aorfi/URA2019/Photos/iteration.docx

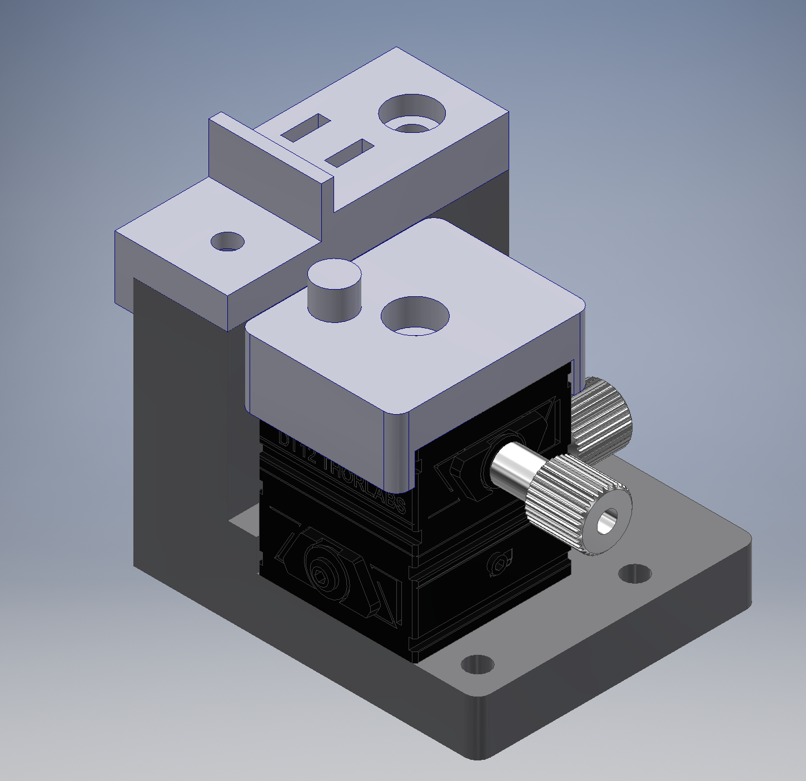
[picture p11: figure]
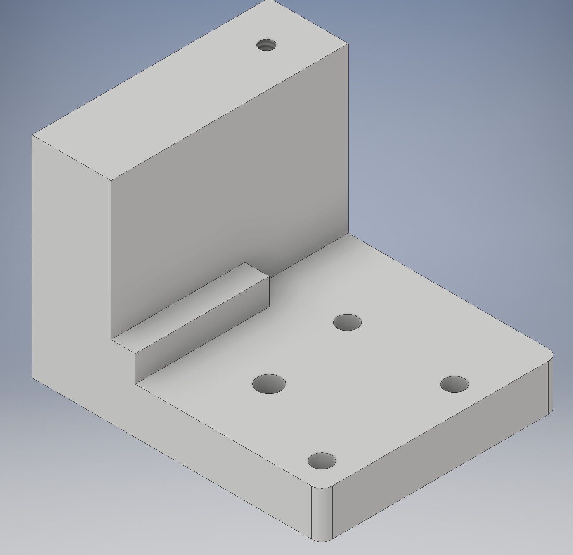
[picture p12: figure]
