aorfi/URA2019/Photos/Version2.docx

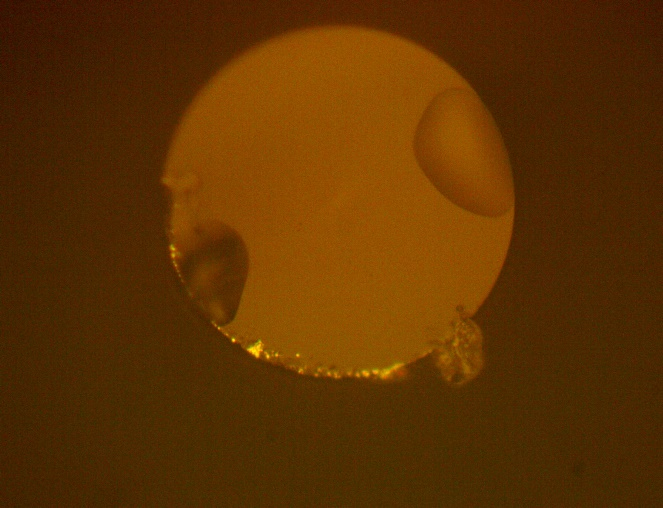
[picture p13: figure]
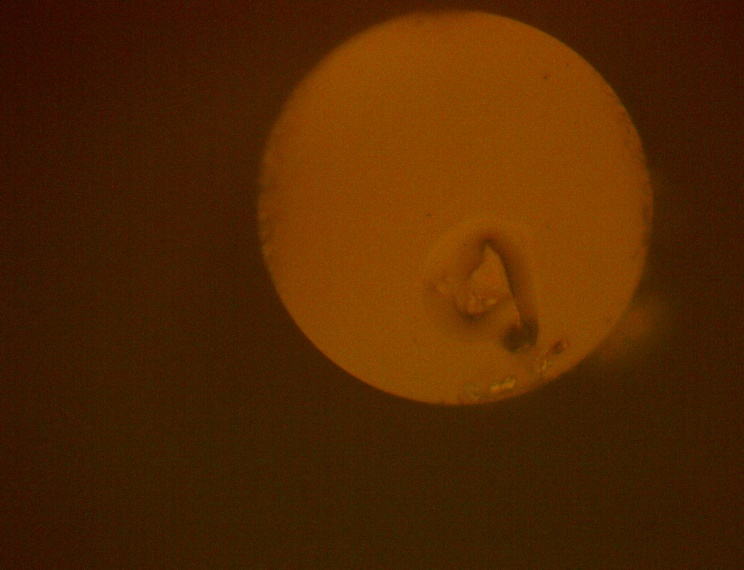
[picture p14: figure]
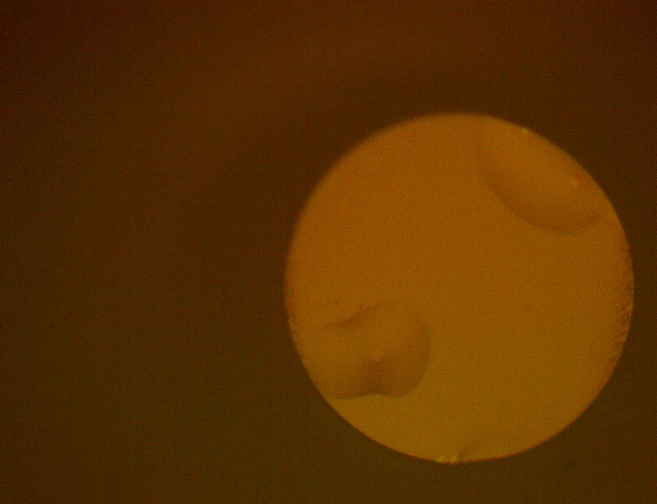
[picture p15: figure]
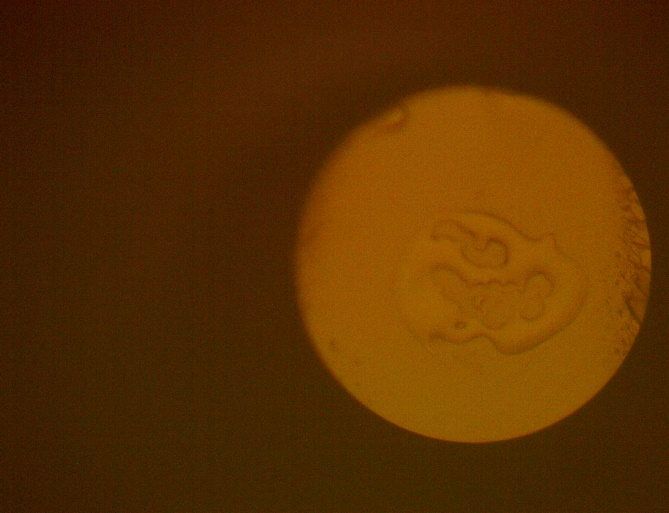
[picture p16: figure]
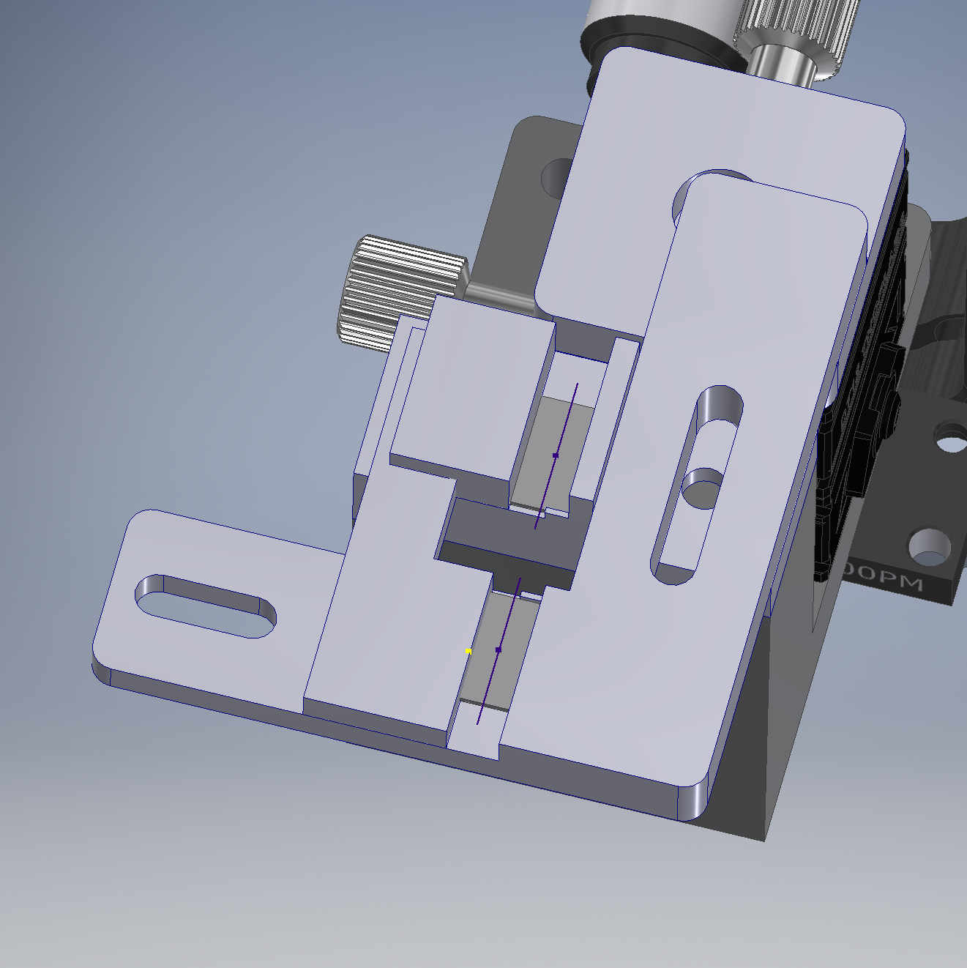
[picture p17: figure]
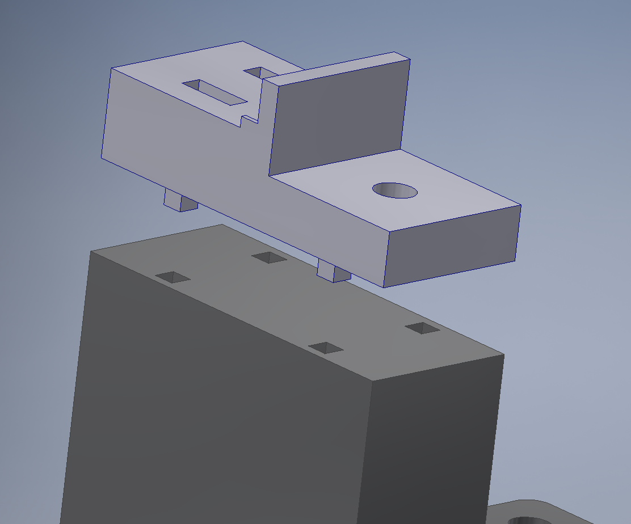
[picture p18: figure]
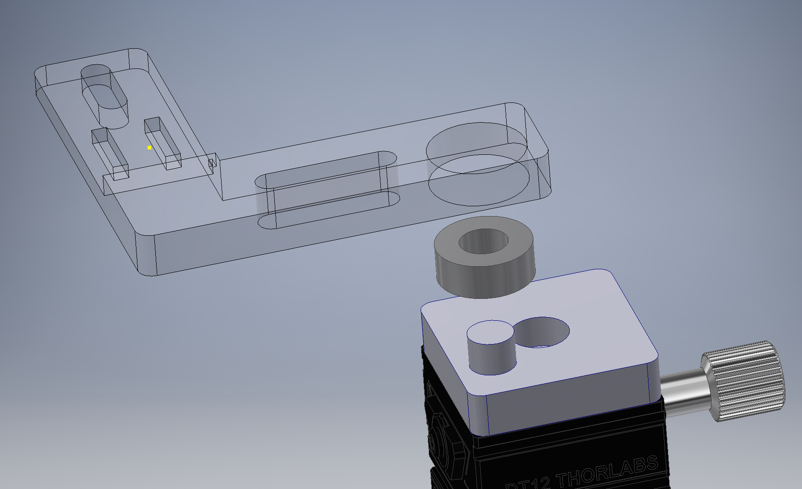
[picture p19: figure]
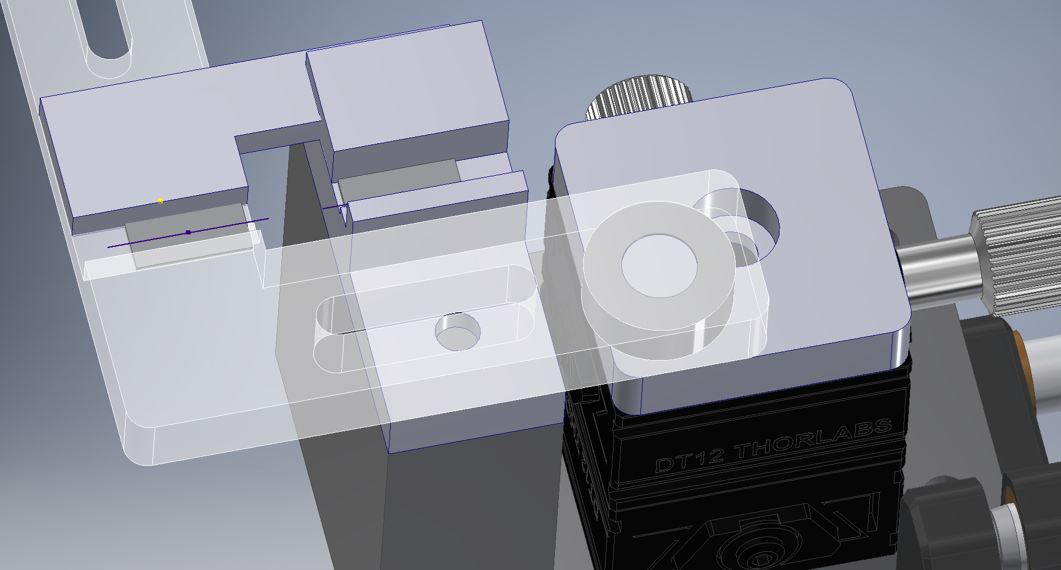
[picture p20: figure]
