aorfi/URA2019/Photos/Epoxy Stamp.docx

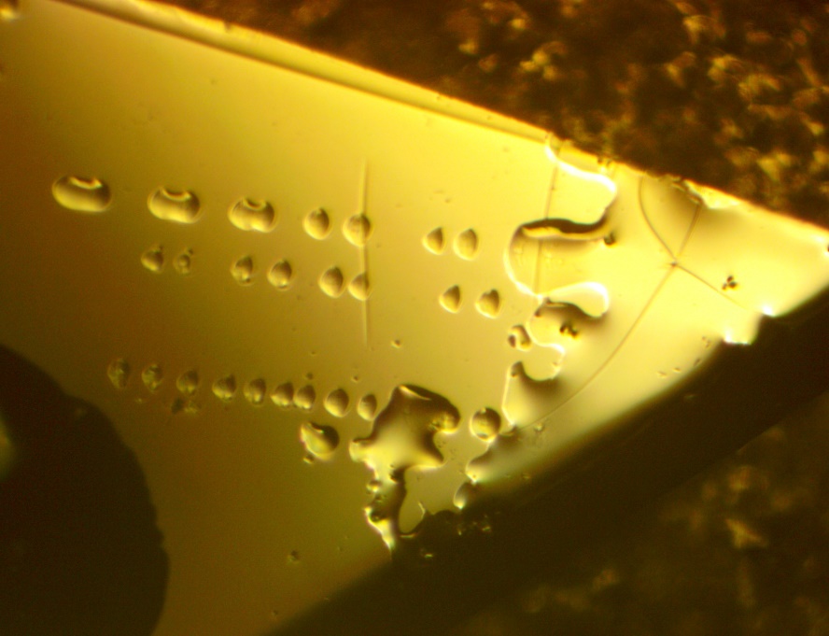
[picture p21: figure]
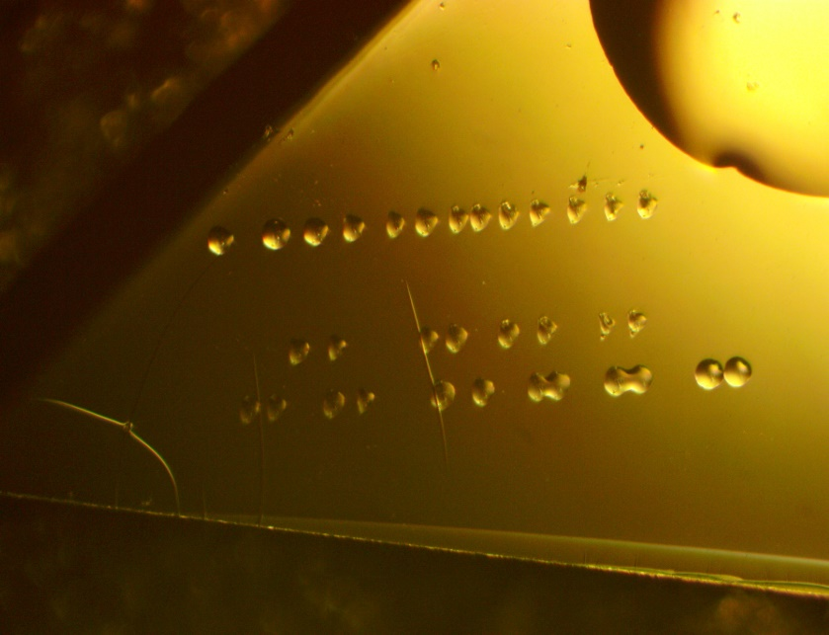
[picture p22: figure]
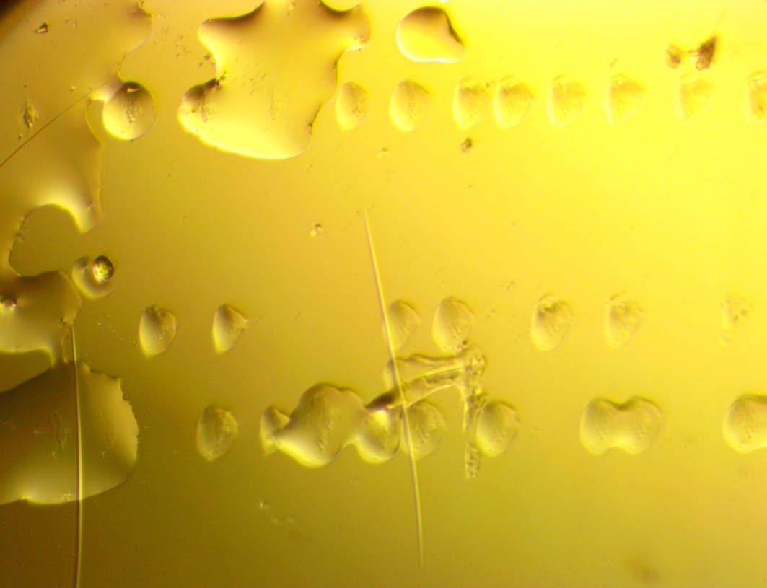
[picture p23: figure]
