aorfi/URA2019/Photos/LabBookPhotos.docx

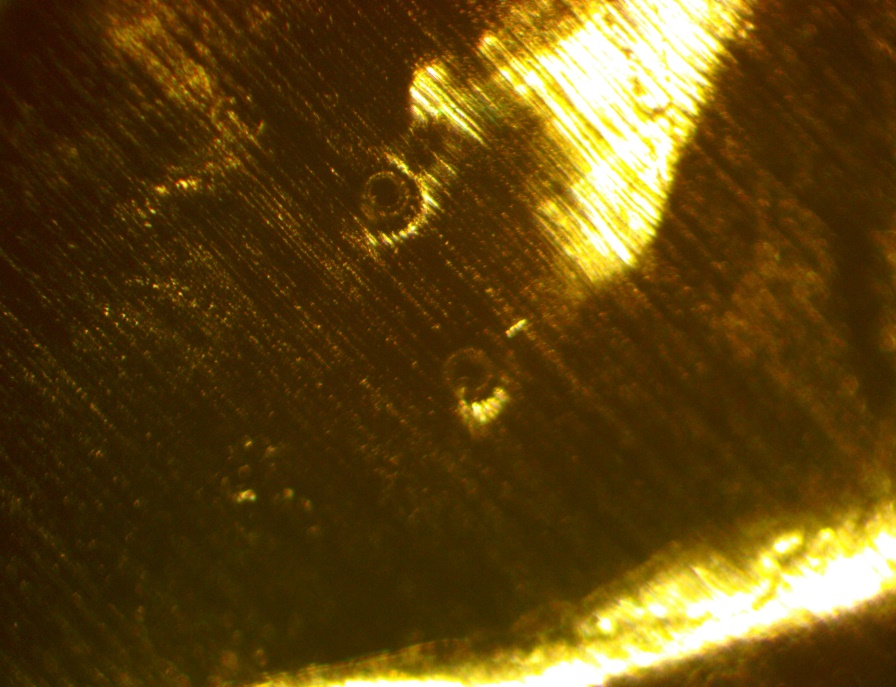
[picture p24: figure]
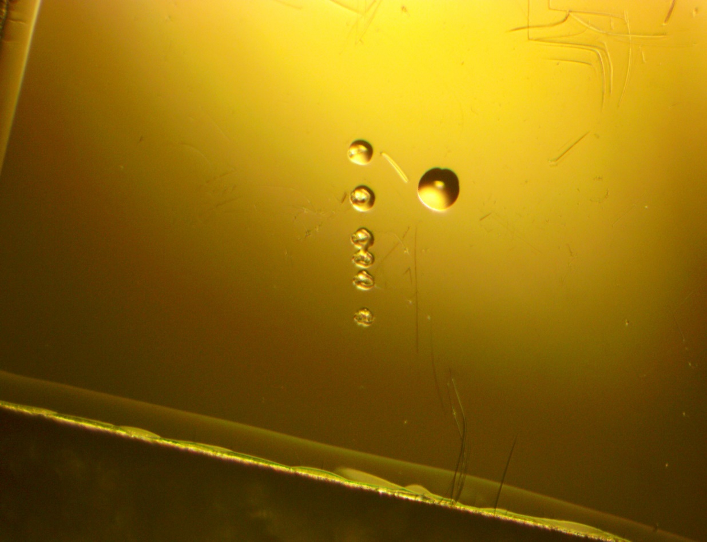
[picture p25: figure]
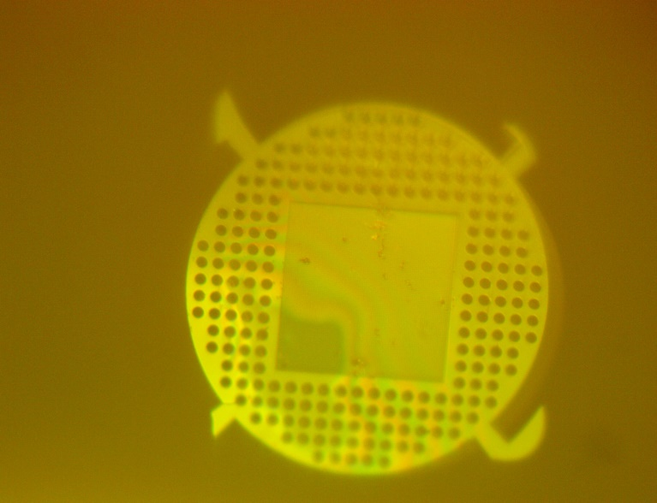
[picture p26: figure]
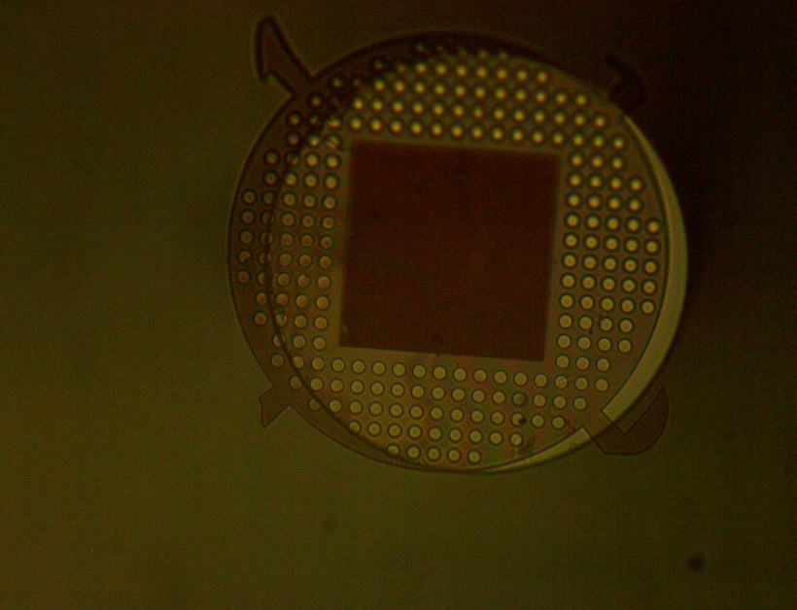
[picture p27: figure]
