aorfi/URA2019/Photos/02-1.jpg

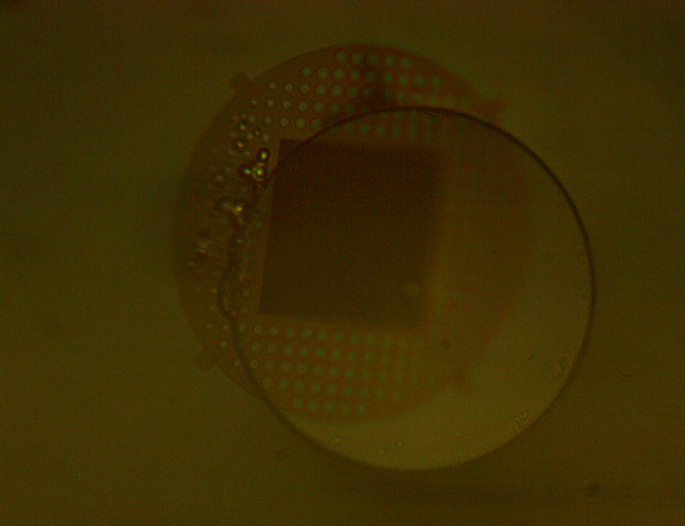
Photos/02-1.jpg
