aorfi/URA2019/Photos/02-2.jpg

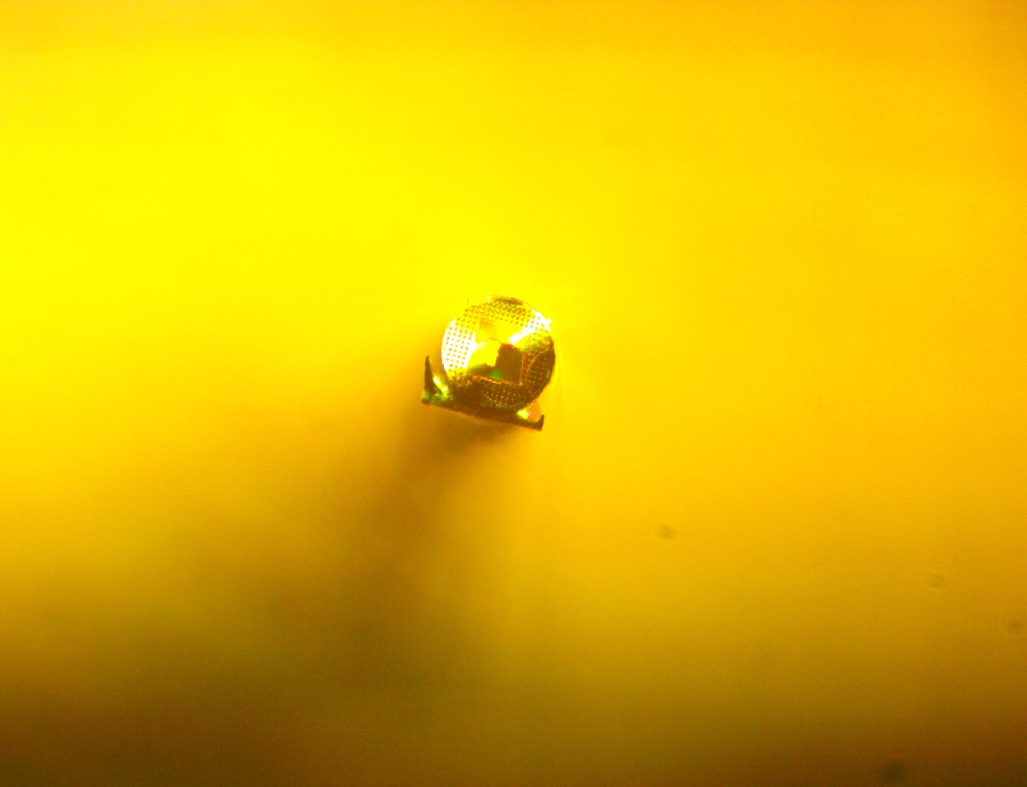
Photos/02-2.jpg
