aorfi/URA2019/Photos/03-1(1).jpg

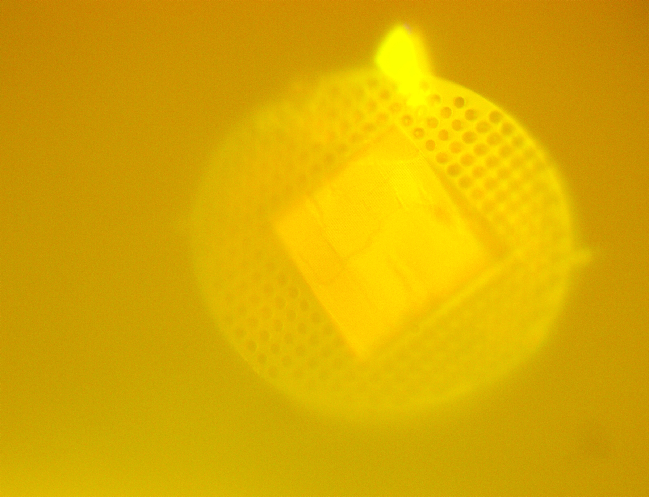
Photos/03-1(1).jpg
