aorfi/URA2019/Photos/03-Broken.jpg

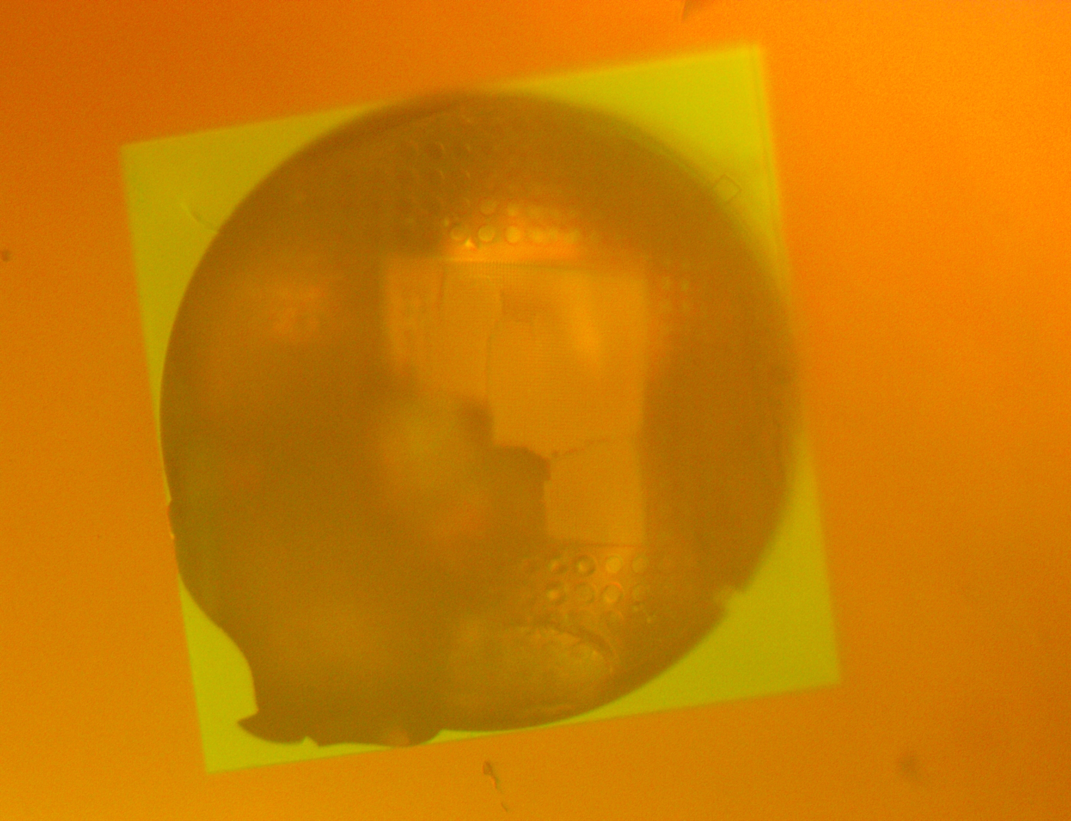
Photos/03-Broken.jpg
