aorfi/URA2019/Photos/aligned.JPG

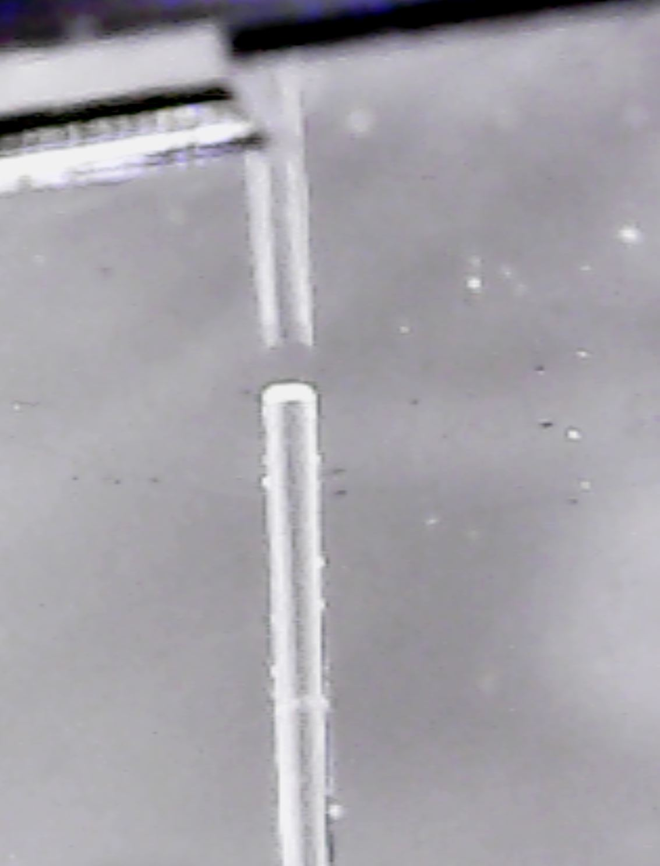
Photos/aligned.JPG
