aorfi/URA2019/Photos/ButtCouplingAfter2.jpg

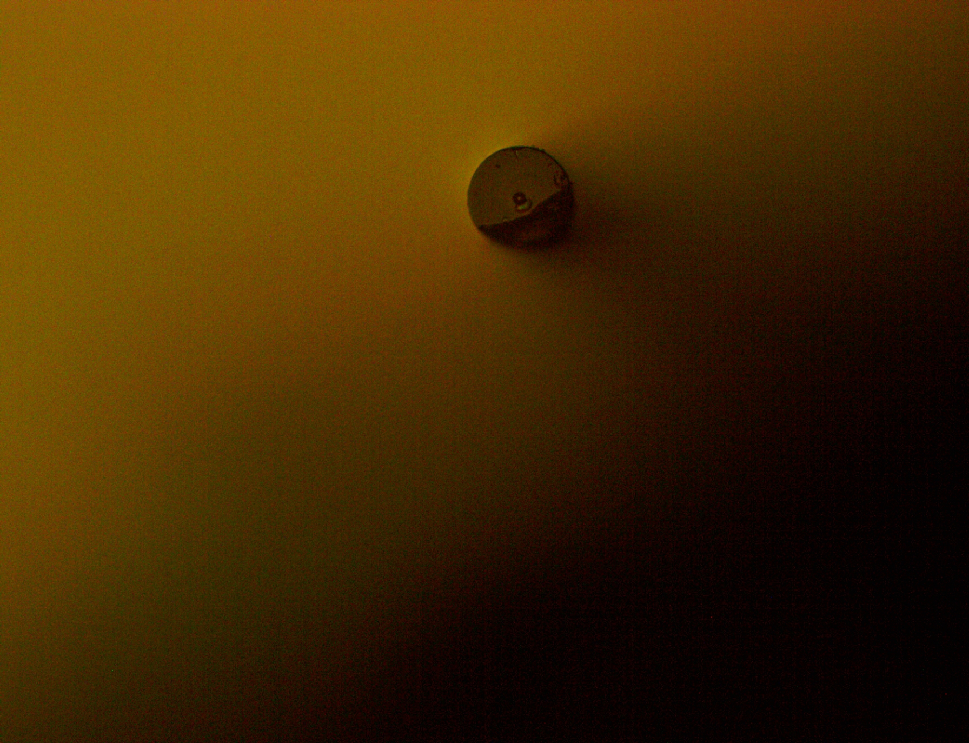
Photos/ButtCouplingAfter2.jpg
