aorfi/URA2019/Photos/ButtCouplingAfter4.jpg

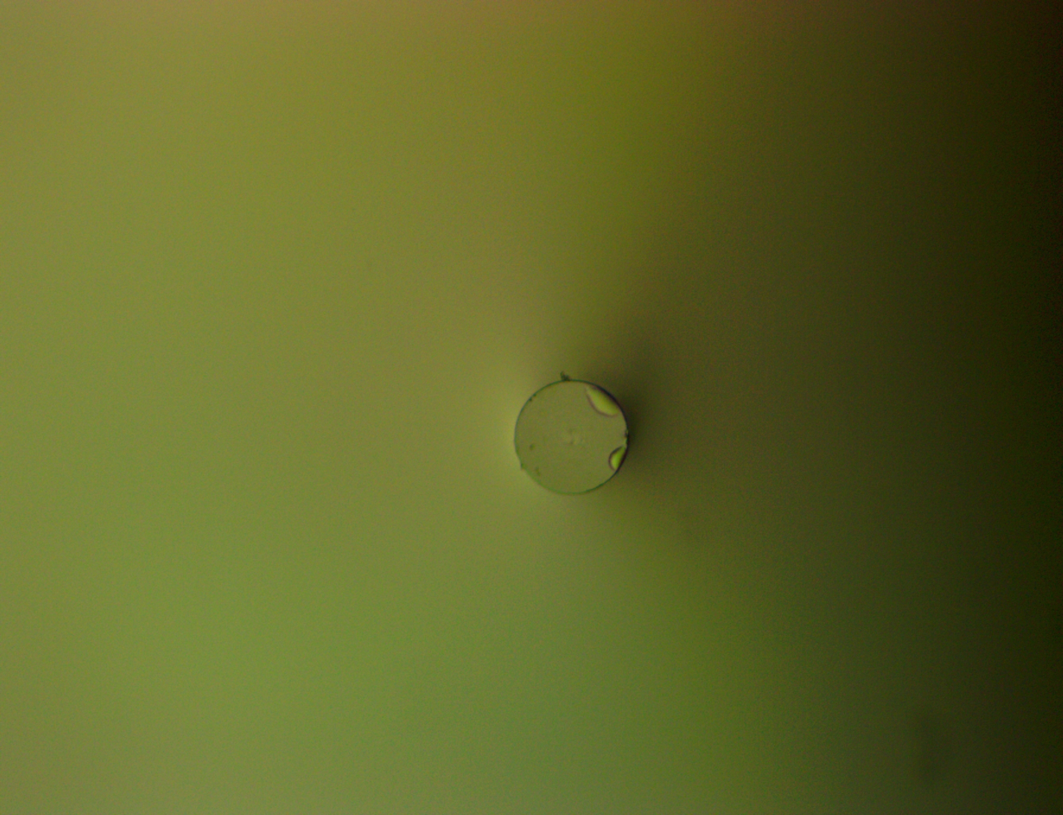
Photos/ButtCouplingAfter4.jpg
