aorfi/URA2019/Photos/ButtCouplingAfter5.jpg

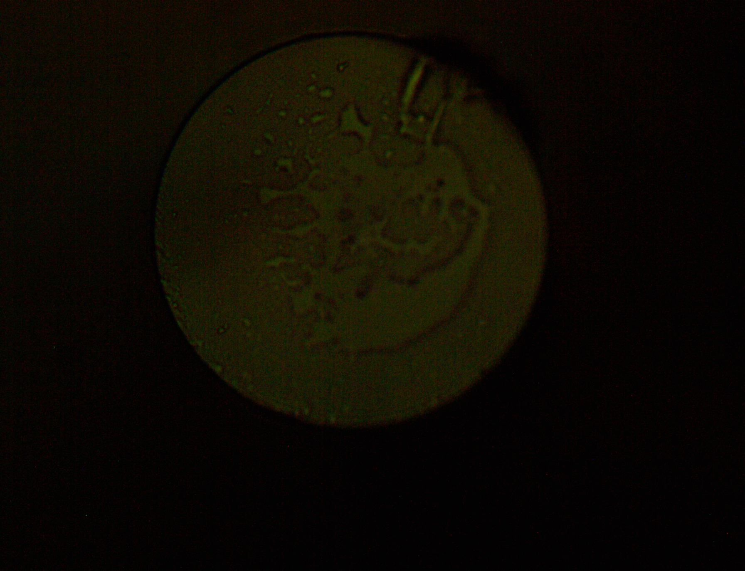
Photos/ButtCouplingAfter5.jpg
