aorfi/URA2019/Photos/ButtCouplingAfter6.jpg

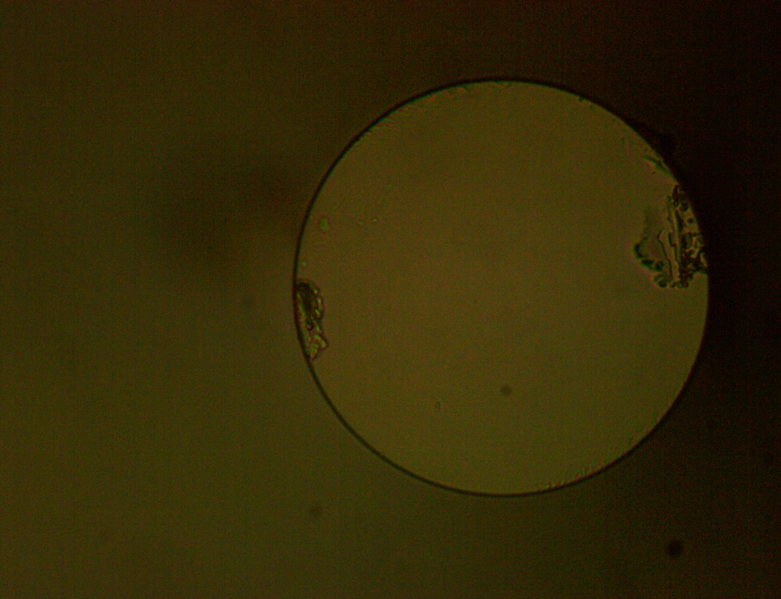
Photos/ButtCouplingAfter6.jpg
