aorfi/URA2019/Photos/ButtCouplingAfter7.jpg

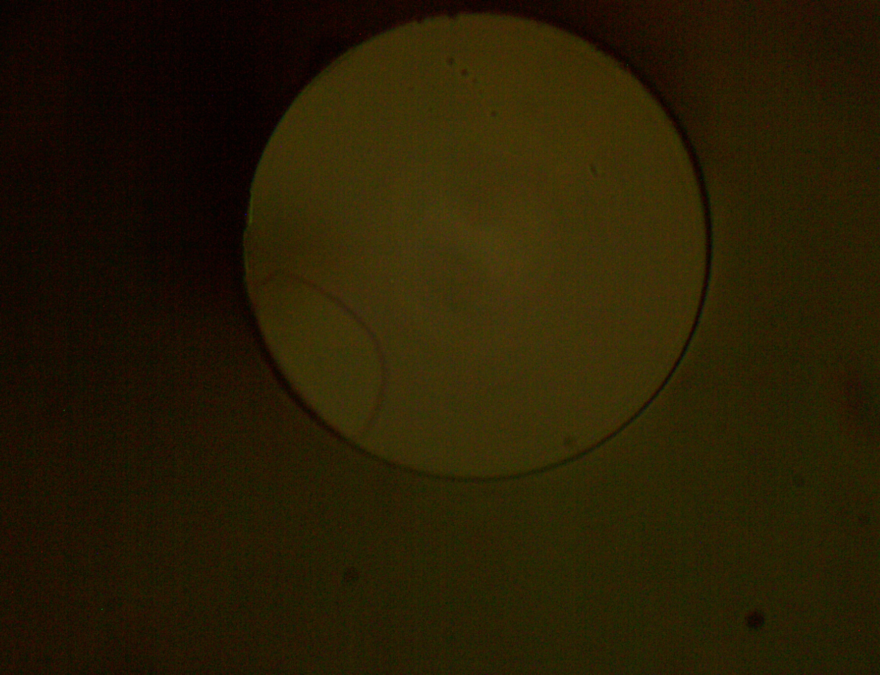
Photos/ButtCouplingAfter7.jpg
