aorfi/URA2019/Photos/ButtCouplingAfter8.jpg

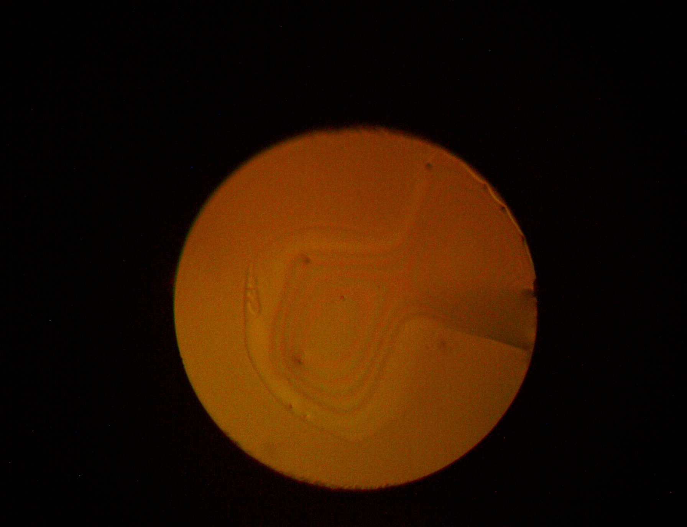
Photos/ButtCouplingAfter8.jpg
