aorfi/URA2019/Photos/ButtCouplingAfter10.jpg

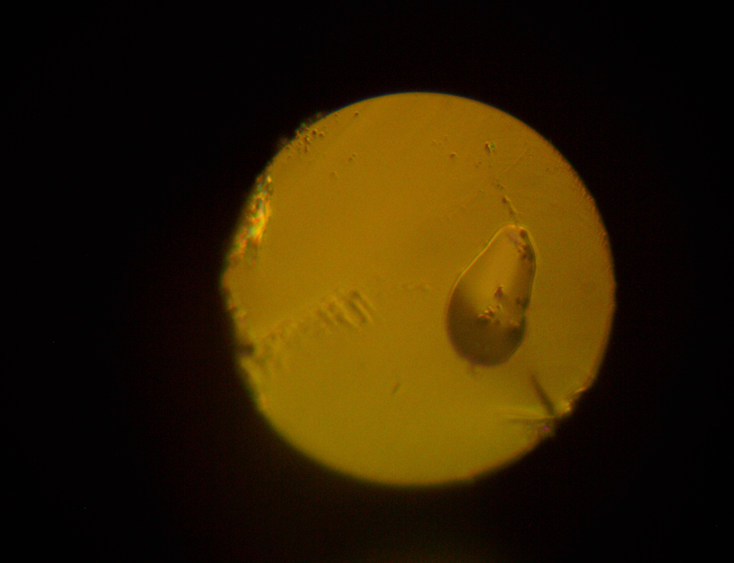
Photos/ButtCouplingAfter10.jpg
