aorfi/URA2019/Photos/ButtCouplingAfter11-1.jpg

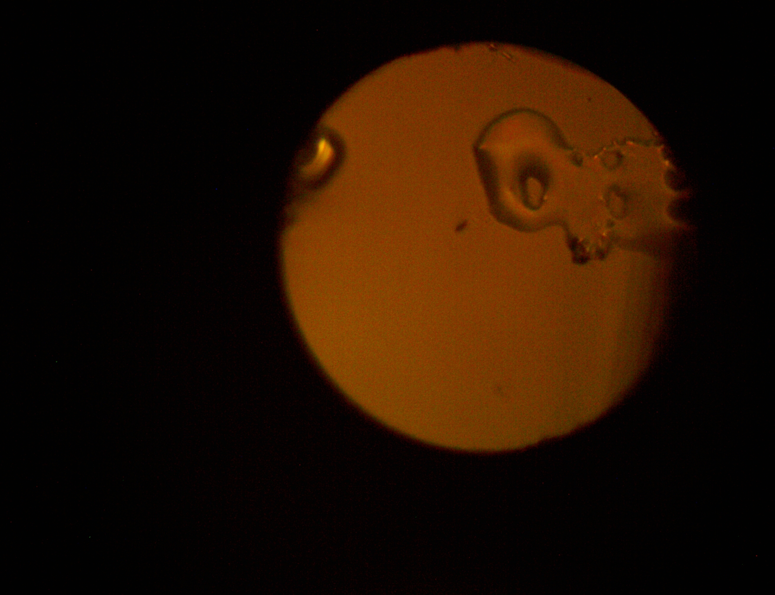
Photos/ButtCouplingAfter11-1.jpg
