aorfi/URA2019/Photos/ButtCouplingAfter11.jpg

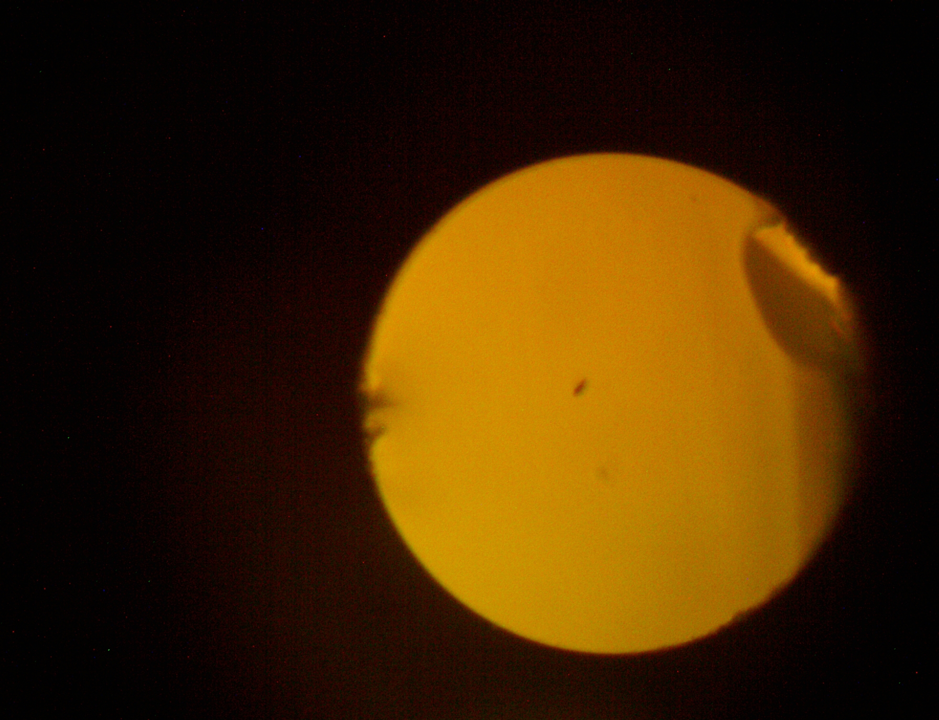
Photos/ButtCouplingAfter11.jpg
