aorfi/URA2019/Photos/ButtCouplingAfter12.jpg

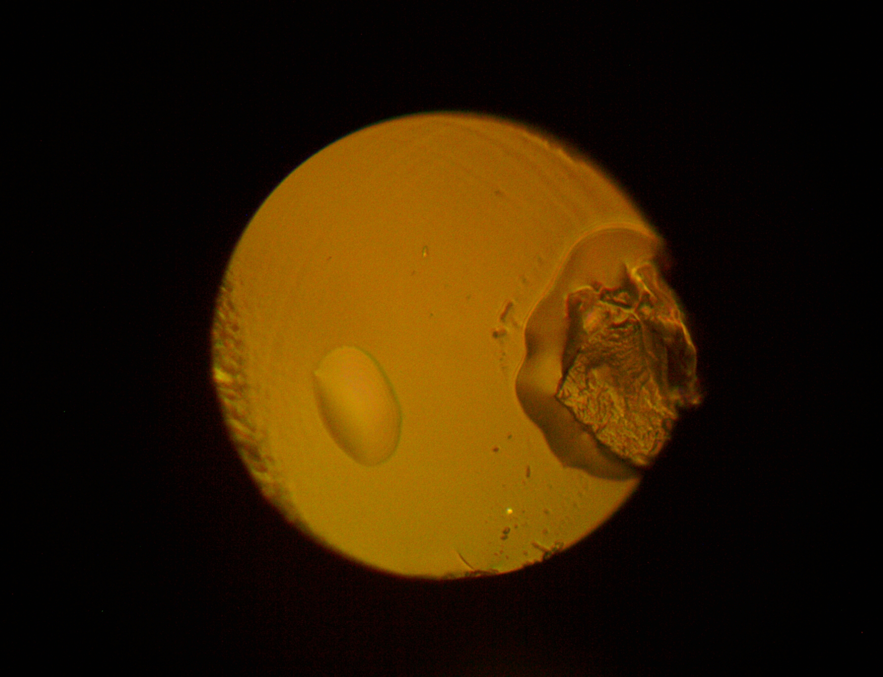
Photos/ButtCouplingAfter12.jpg
