aorfi/URA2019/Photos/ButtCouplingAfter13.jpg

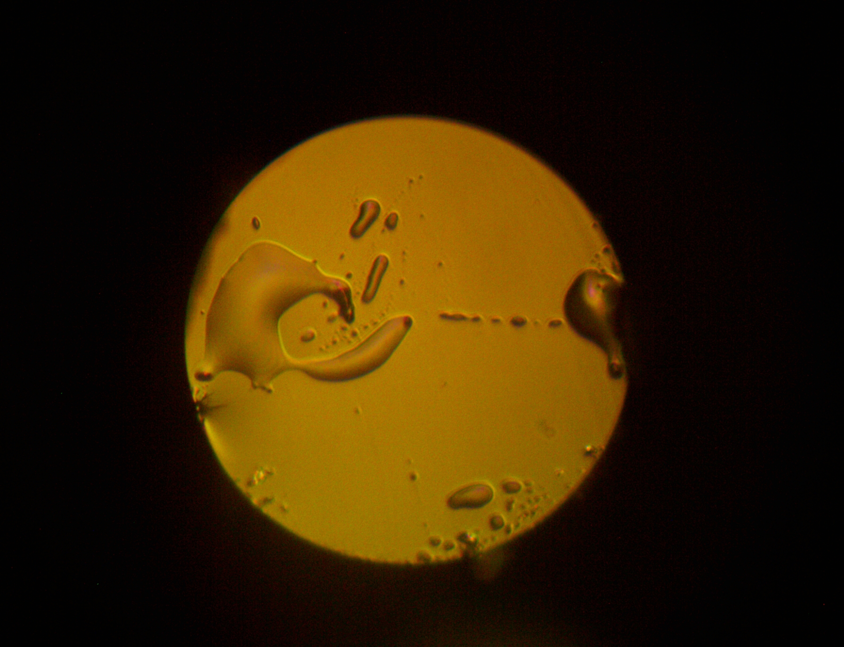
Photos/ButtCouplingAfter13.jpg
