aorfi/URA2019/Photos/ButtCouplingAfter14.jpg

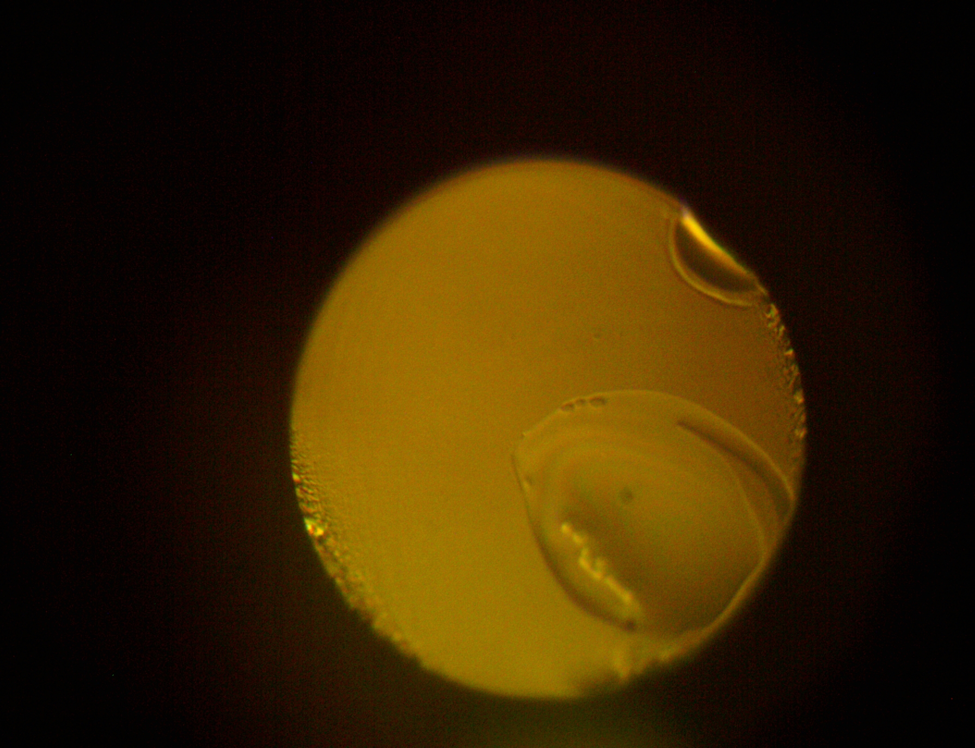
Photos/ButtCouplingAfter14.jpg
