aorfi/URA2019/Photos/ButtCouplingAfter15.jpg

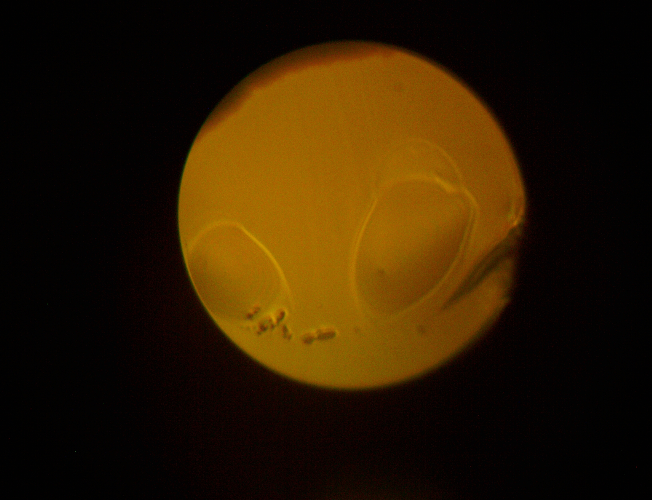
Photos/ButtCouplingAfter15.jpg
