aorfi/URA2019/Photos/ButtCouplingAfter16.jpg

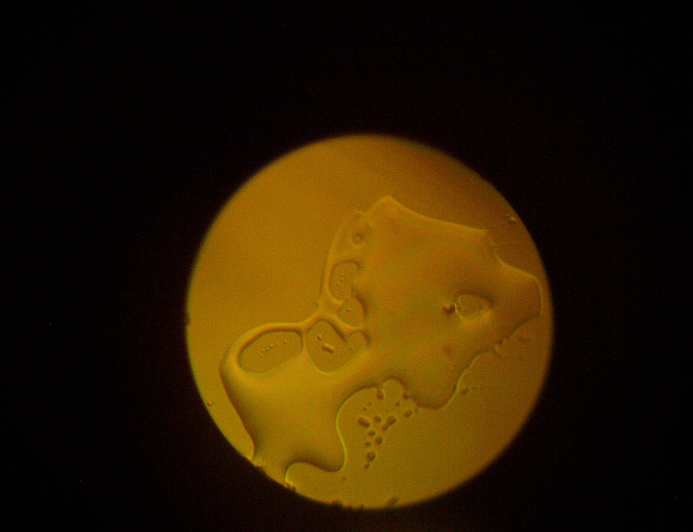
Photos/ButtCouplingAfter16.jpg
