aorfi/URA2019/Photos/ButtCouplingBefore5.jpg

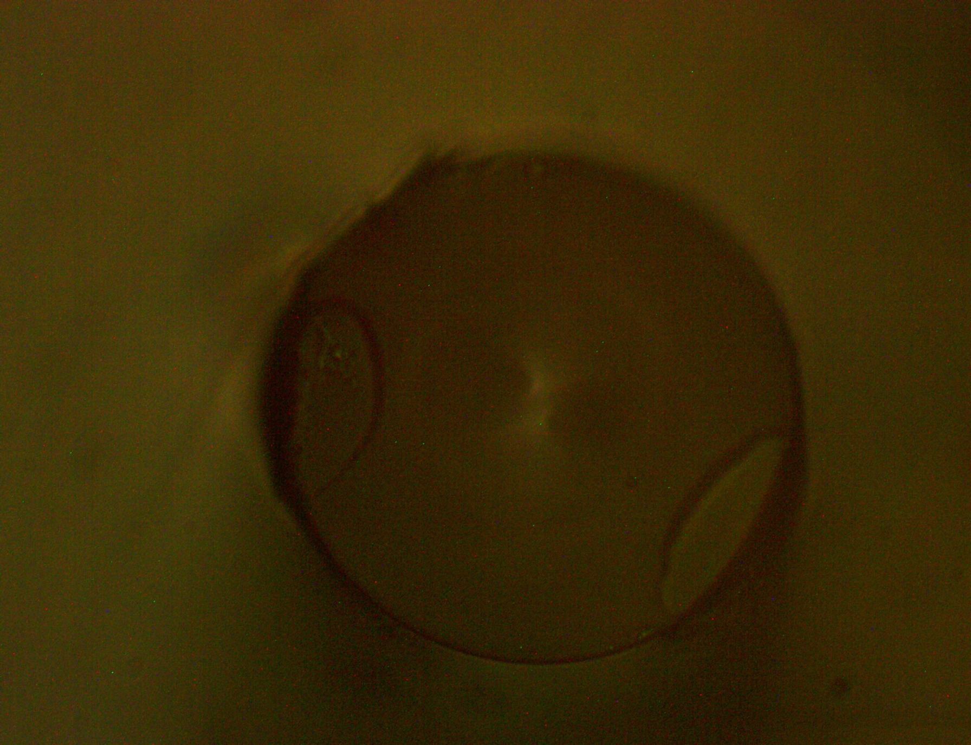
Photos/ButtCouplingBefore5.jpg
