aorfi/URA2019/Photos/ButtCouplingBefore6.jpg

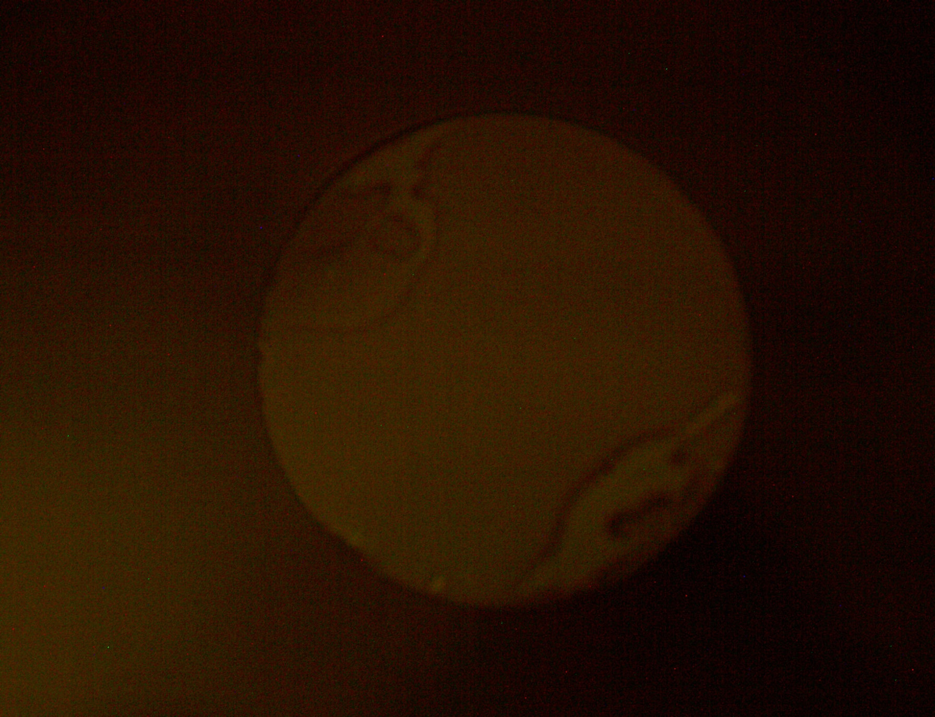
Photos/ButtCouplingBefore6.jpg
