aorfi/URA2019/Photos/ButtCouplingBefore7.jpg

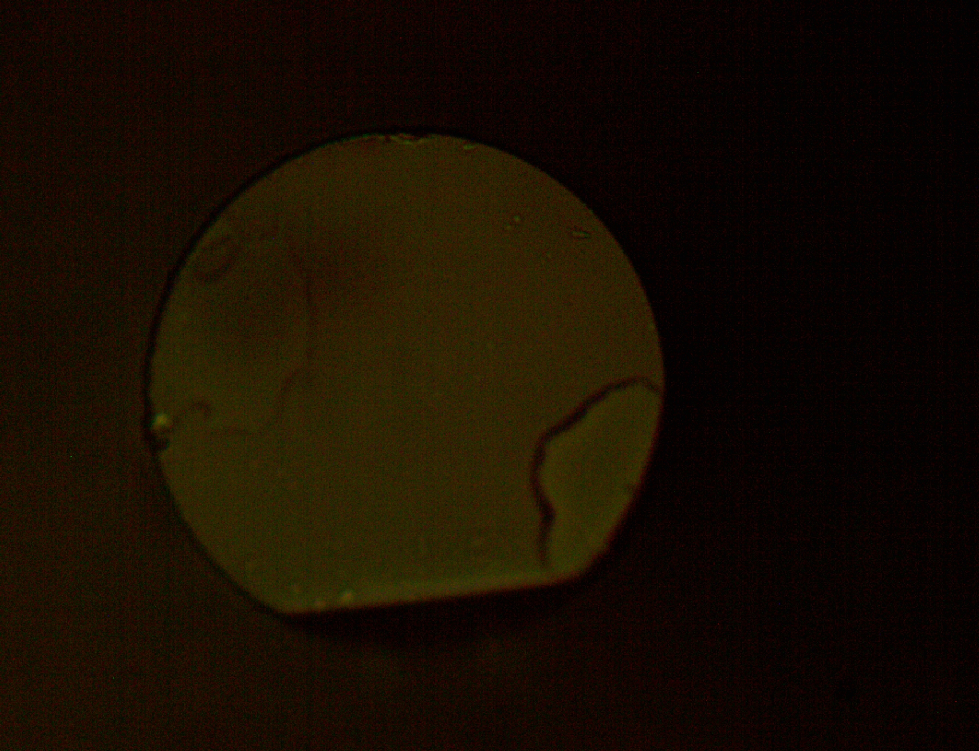
Photos/ButtCouplingBefore7.jpg
