aorfi/URA2019/Photos/ButtCouplingBefore8.jpg

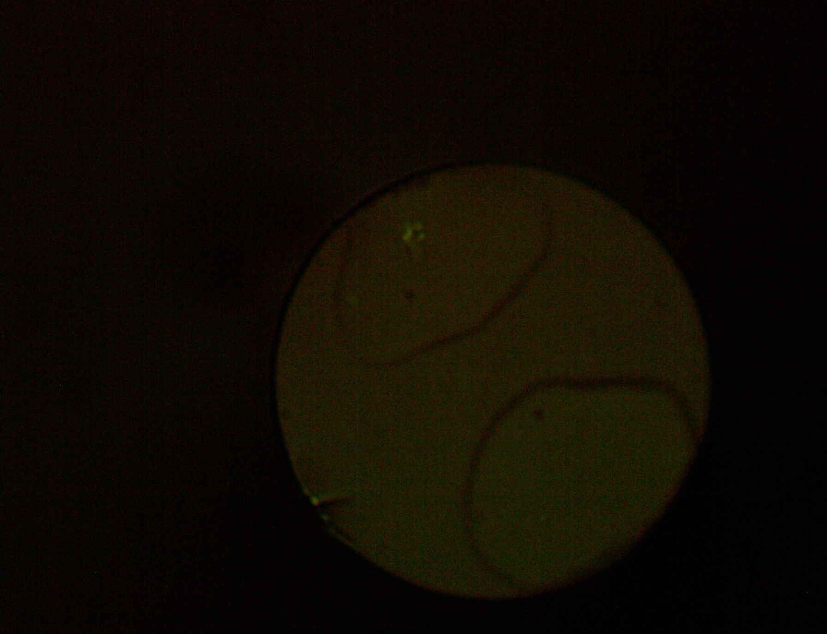
Photos/ButtCouplingBefore8.jpg
