aorfi/URA2019/Photos/ButtCouplingBefore10.jpg

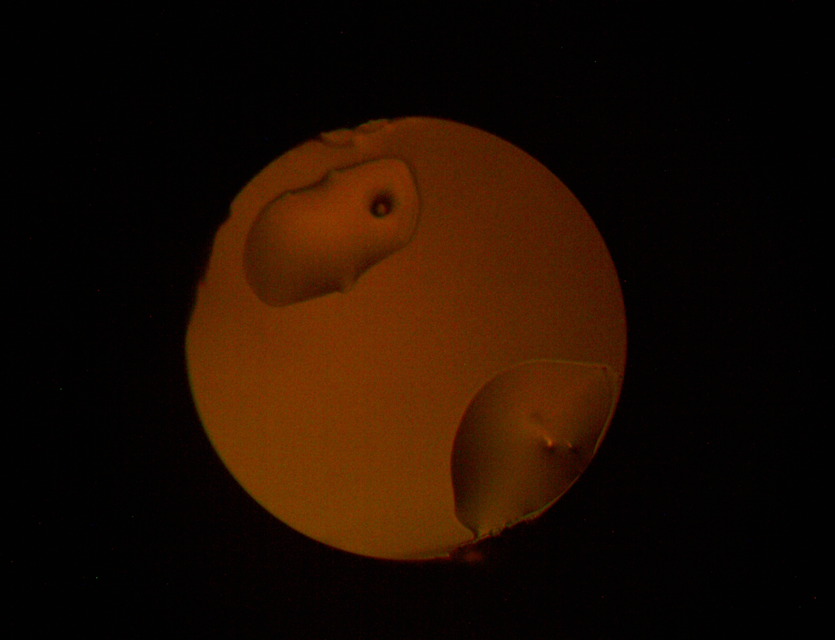
Photos/ButtCouplingBefore10.jpg
