aorfi/URA2019/Photos/ButtCouplingBefore11.jpg

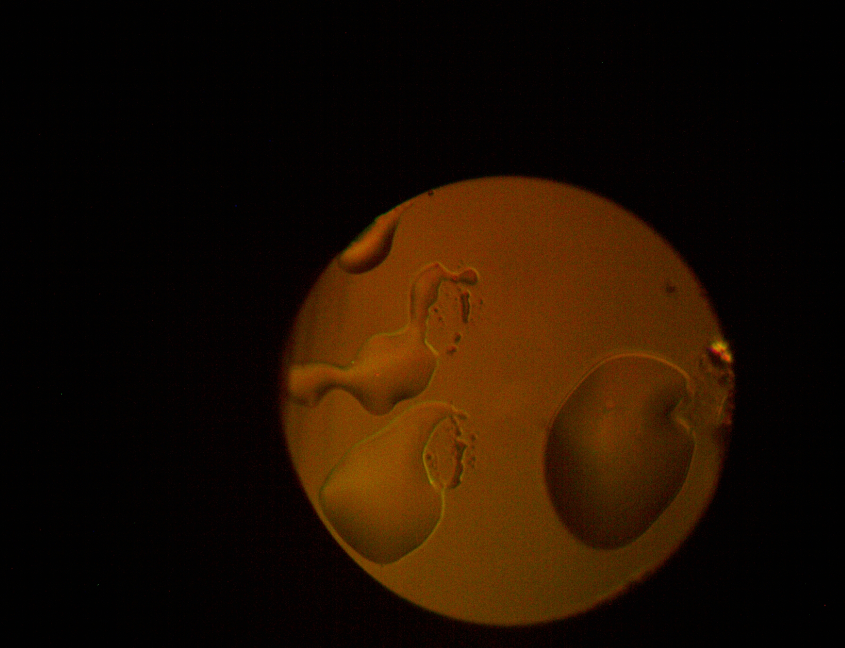
Photos/ButtCouplingBefore11.jpg
