aorfi/URA2019/Photos/ButtCouplingBefore15.jpg

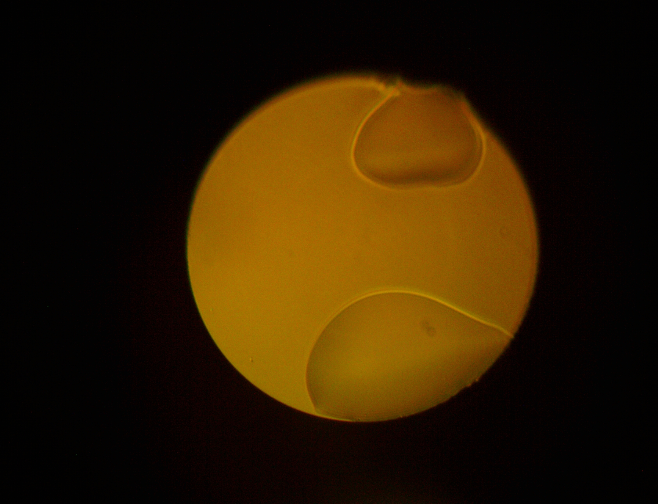
Photos/ButtCouplingBefore15.jpg
