aorfi/URA2019/Photos/ButtCouplingBefore16.jpg

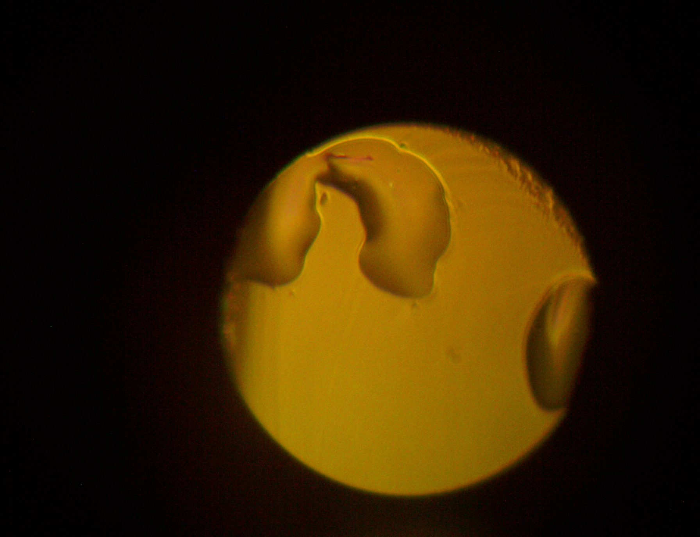
Photos/ButtCouplingBefore16.jpg
