aorfi/URA2019/Photos/camera2 .PNG

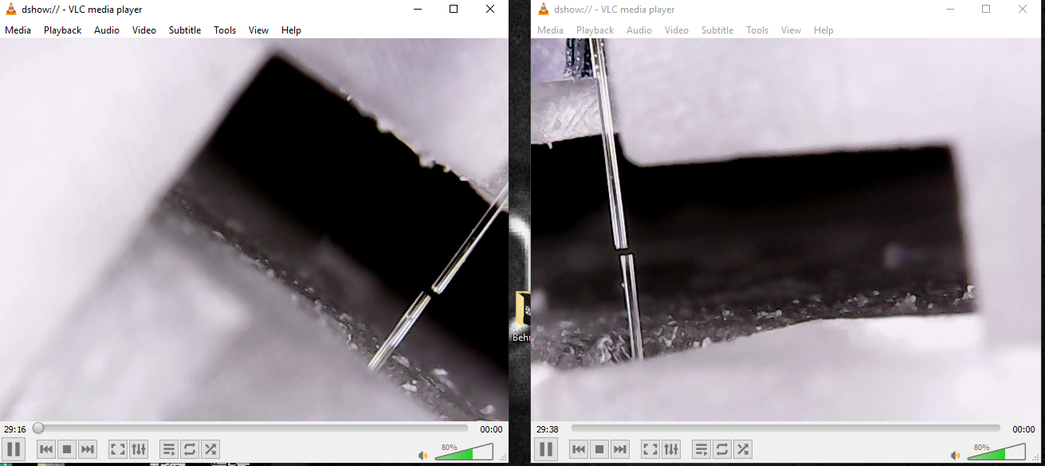
Photos/camera2 .PNG
