aorfi/URA2019/Photos/CanSeeMirror.JPG

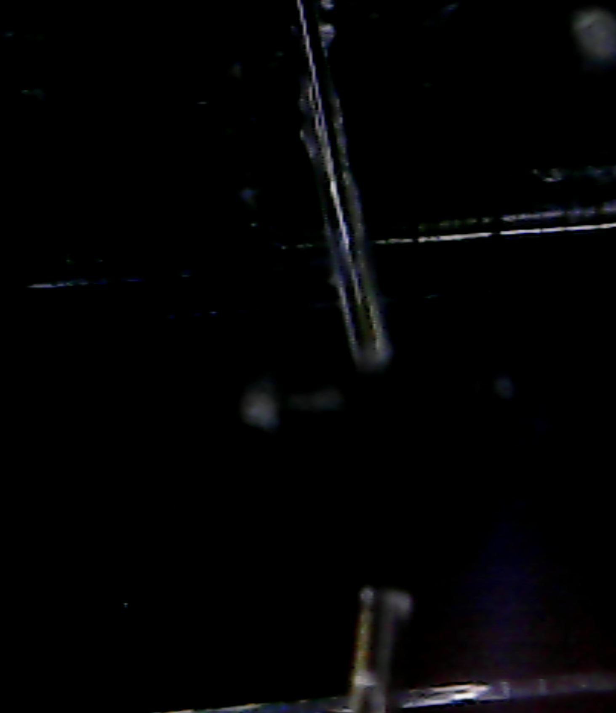
Photos/CanSeeMirror.JPG
