aorfi/URA2019/Photos/Cure_130.jpg

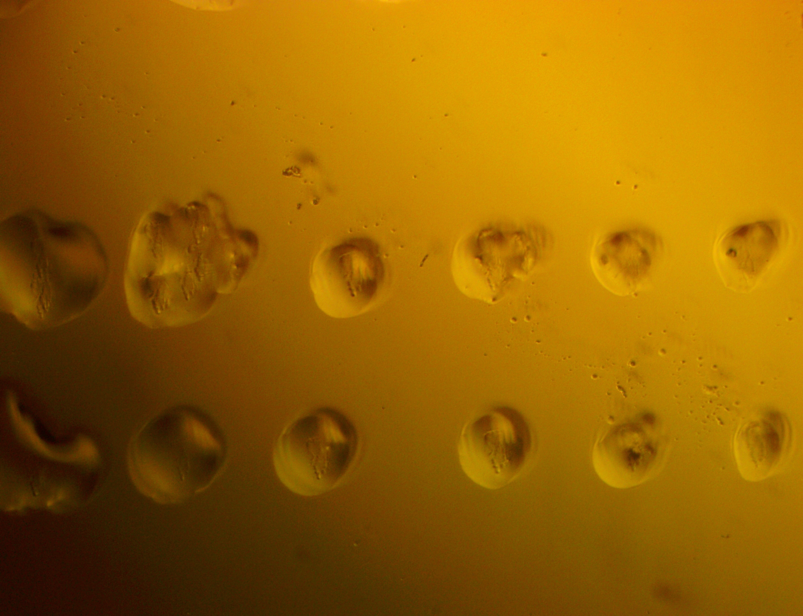
Photos/Cure_130.jpg
