aorfi/URA2019/Photos/Cure_230.jpg

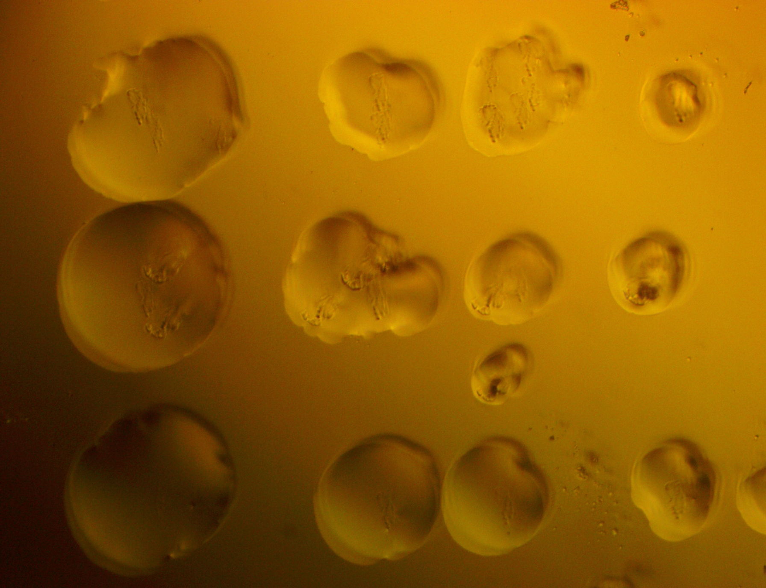
Photos/Cure_230.jpg
