aorfi/URA2019/Photos/Cure_1130.jpg

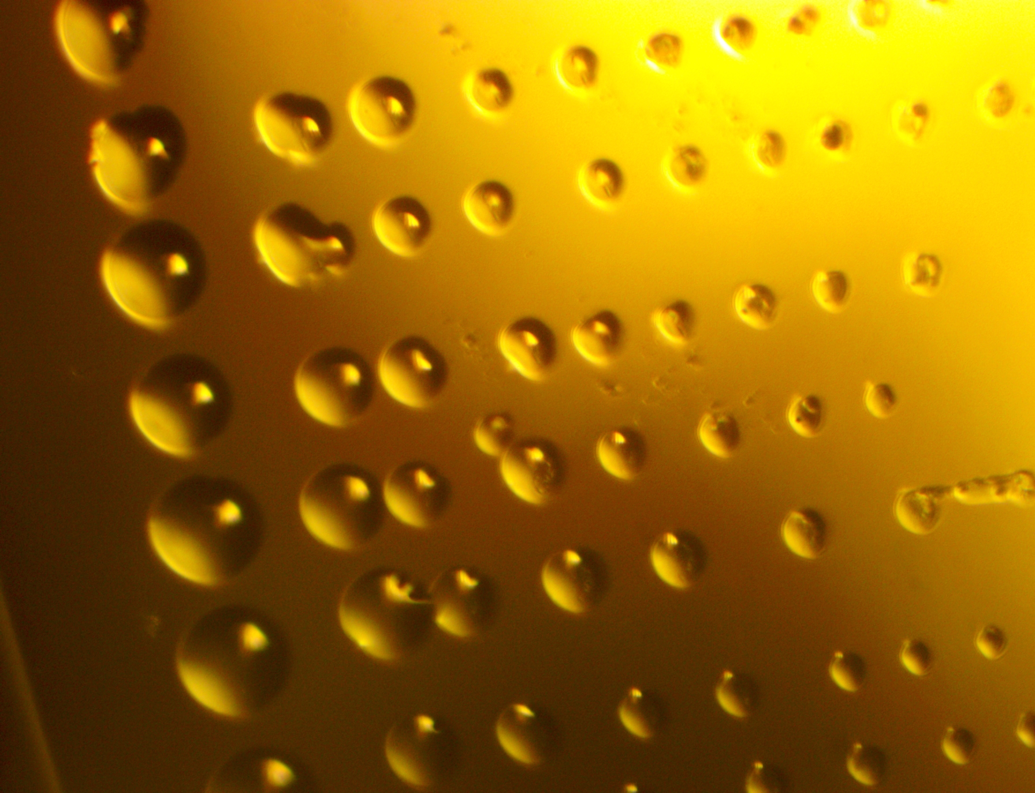
Photos/Cure_1130.jpg
