aorfi/URA2019/Photos/DirectFiberDots1.jpg

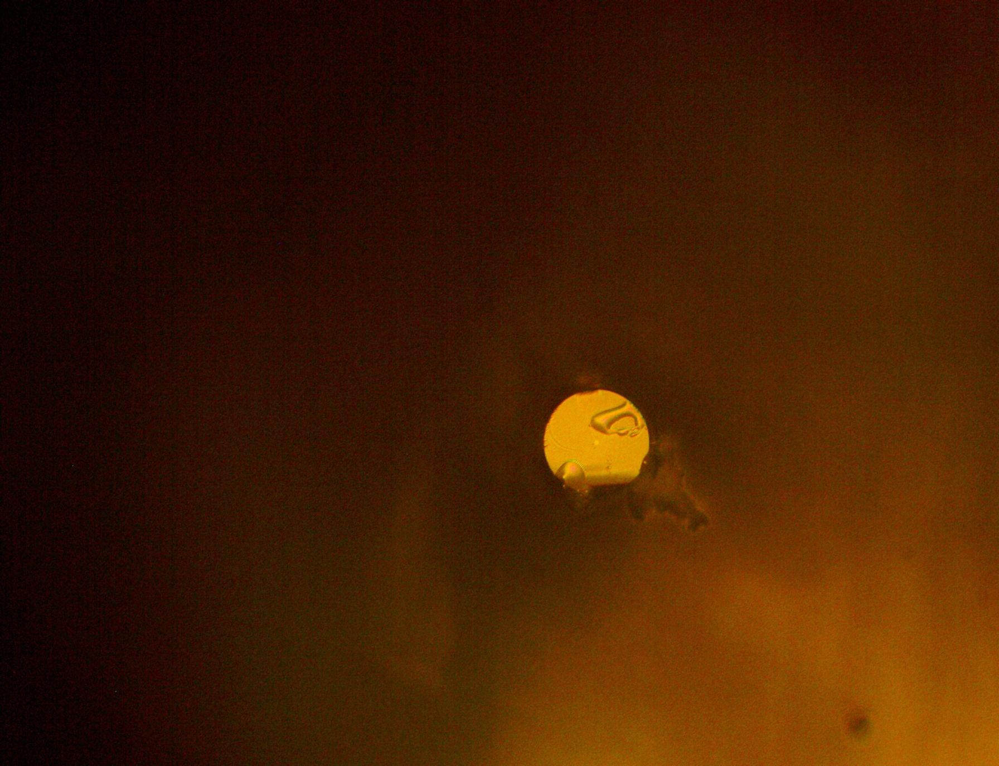
Photos/DirectFiberDots1.jpg
