aorfi/URA2019/Photos/DirectFiberDots6.jpg

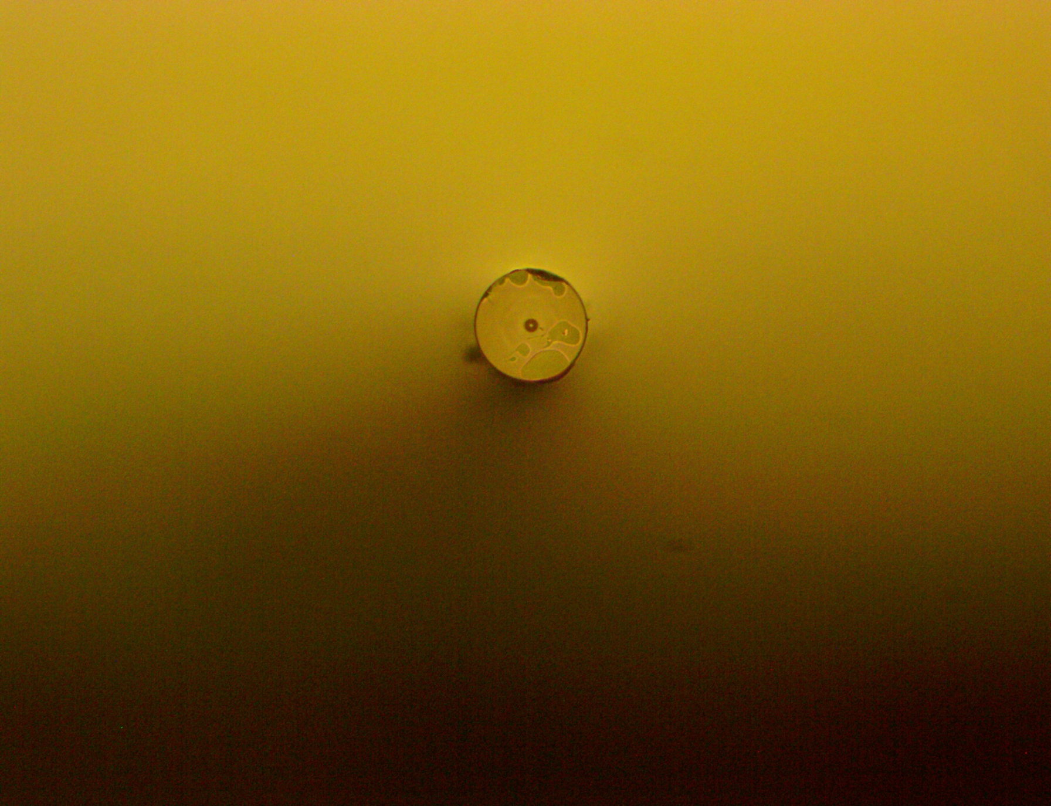
Photos/DirectFiberDots6.jpg
