aorfi/URA2019/Photos/InitialCADv1.JPG

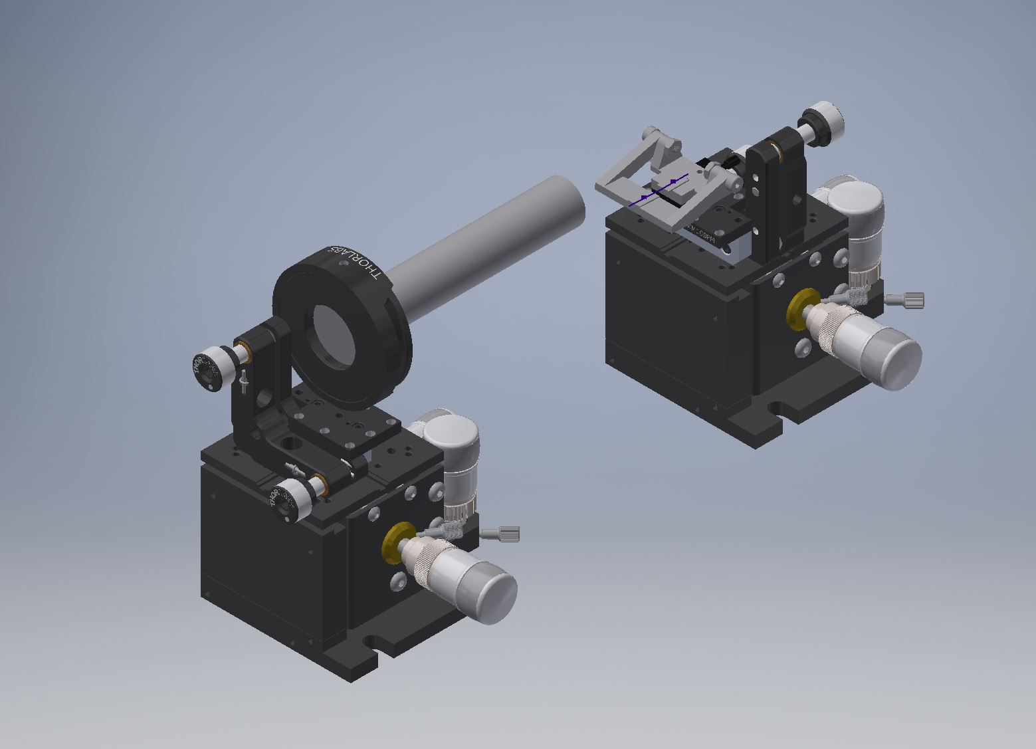
Photos/InitialCADv1.JPG
