aorfi/URA2019/Photos/InitialCADv2.JPG

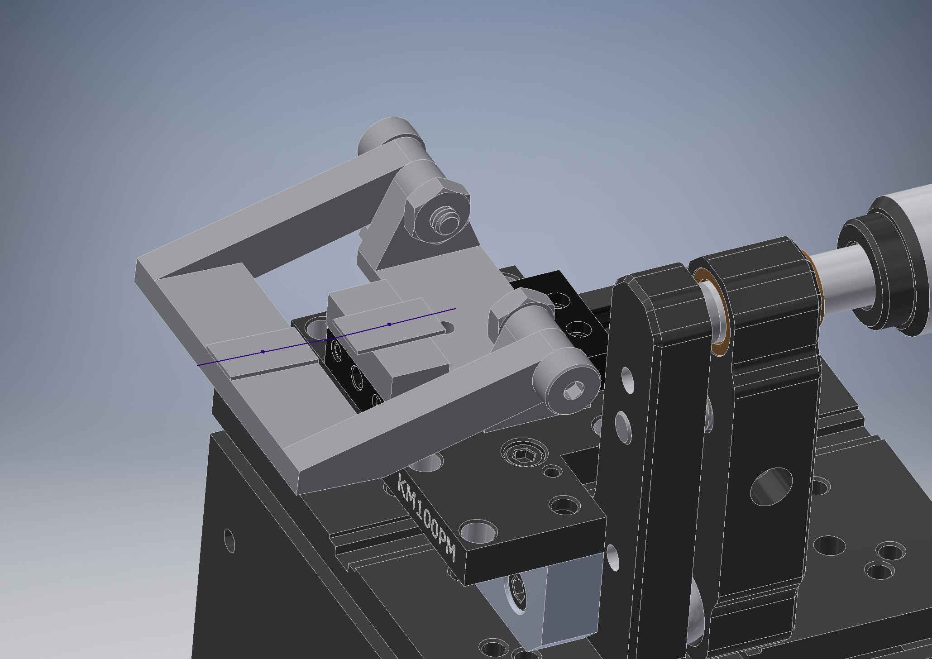
Photos/InitialCADv2.JPG
