aorfi/URA2019/Photos/InitialCADv3.JPG

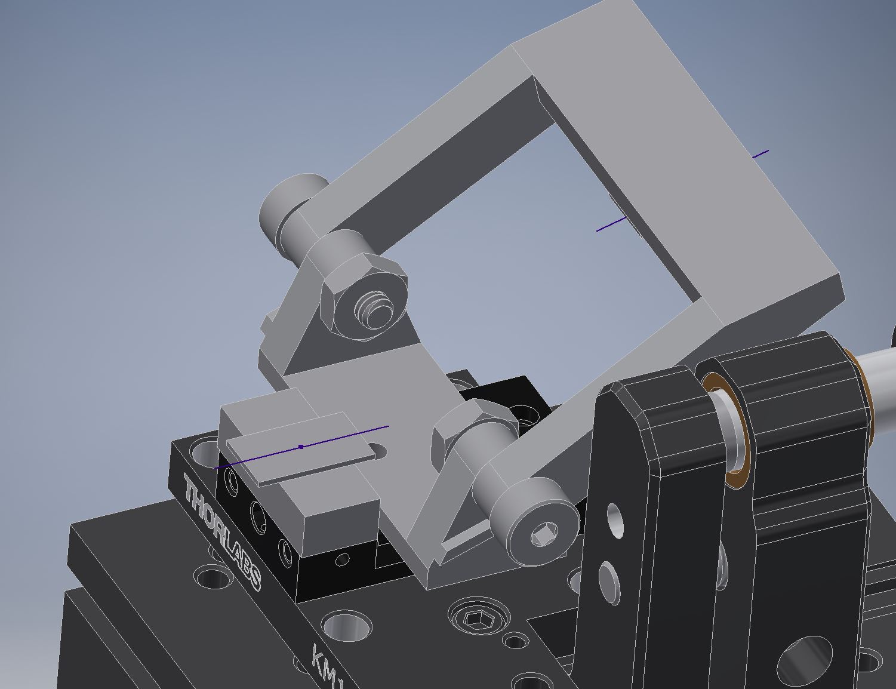
Photos/InitialCADv3.JPG
