aorfi/URA2019/Photos/misaligned.JPG

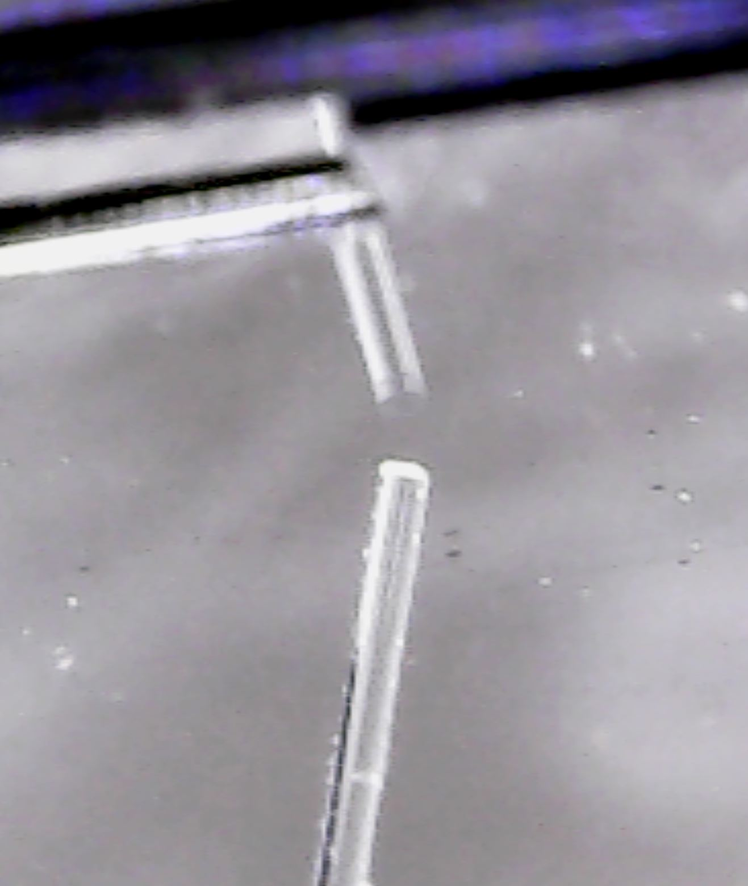
Photos/misaligned.JPG
