aorfi/URA2019/Photos/NP-1-2.jpg

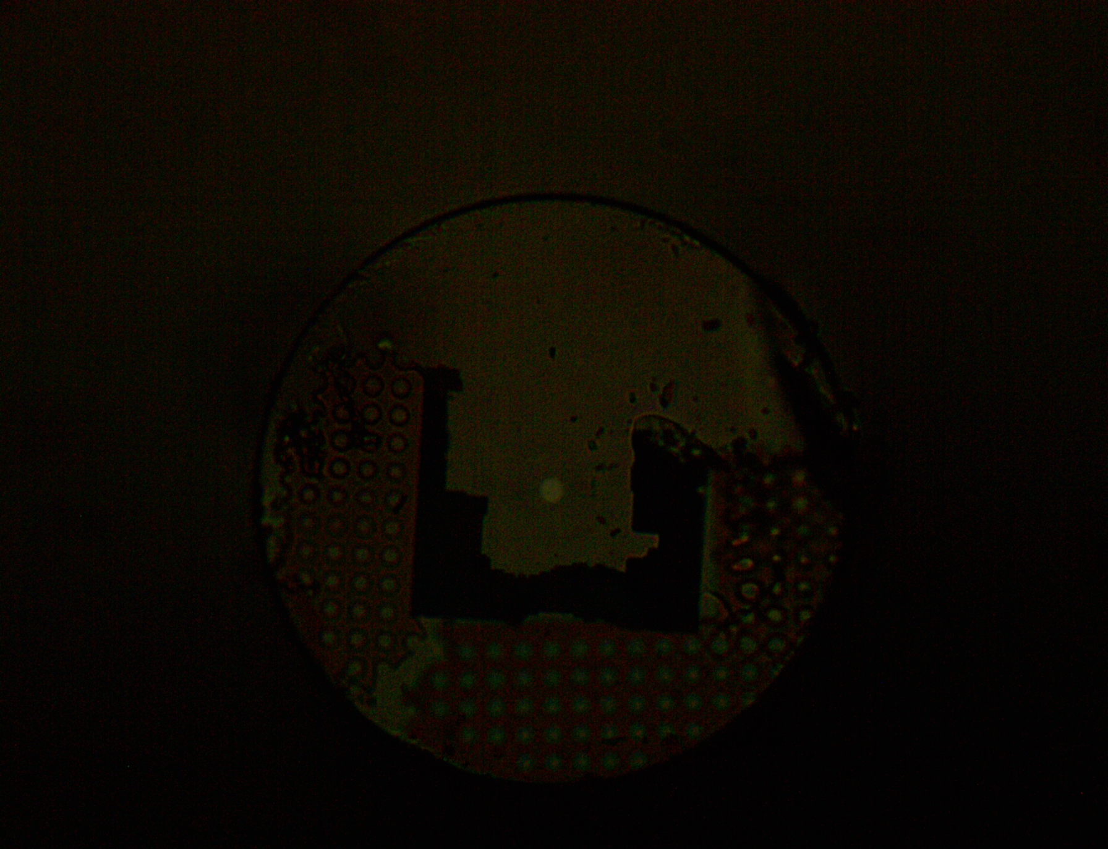
Photos/NP-1-2.jpg
