aorfi/URA2019/Photos/NP-1-3.jpg

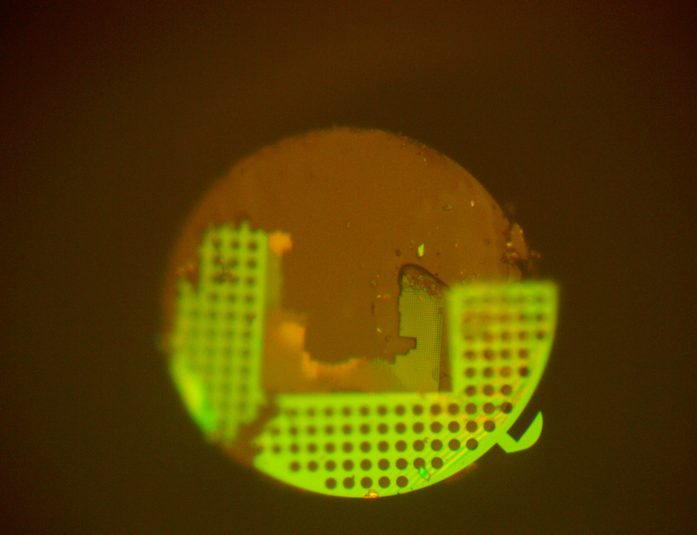
Photos/NP-1-3.jpg
