aorfi/URA2019/Photos/NP-2.jpg

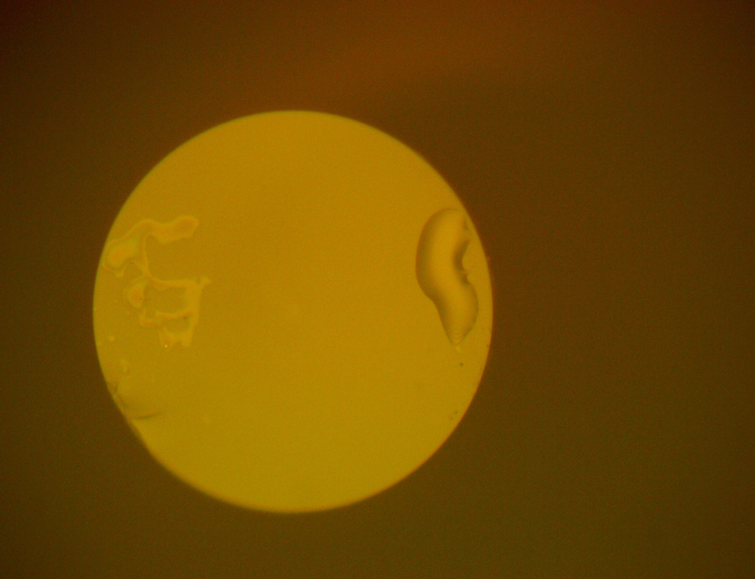
Photos/NP-2.jpg
