aorfi/URA2019/Photos/RemovableDesign1-2.jpg

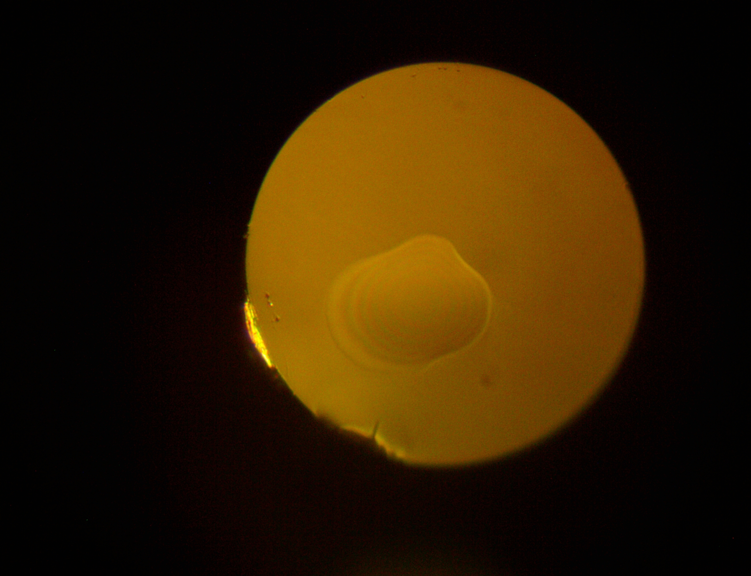
Photos/RemovableDesign1-2.jpg
