aorfi/URA2019/Photos/RemovableDesign2-1.jpg

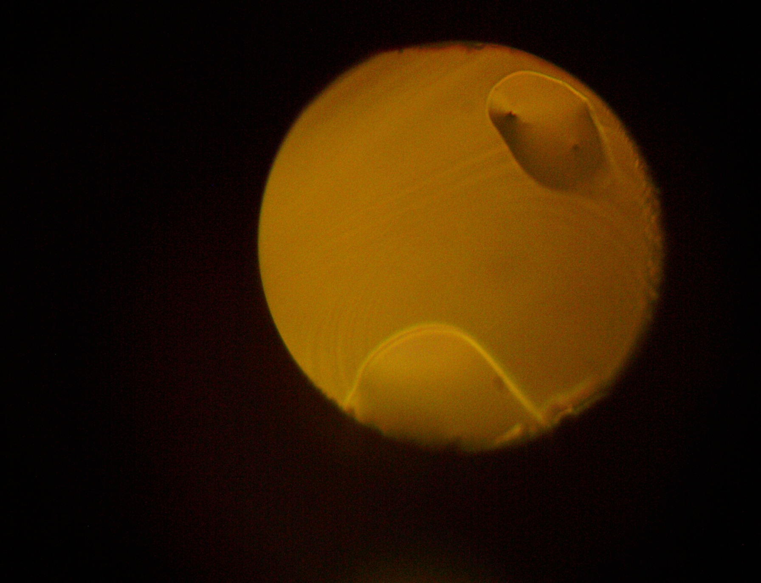
Photos/RemovableDesign2-1.jpg
