aorfi/URA2019/Photos/RemovableDesign4-1.jpg

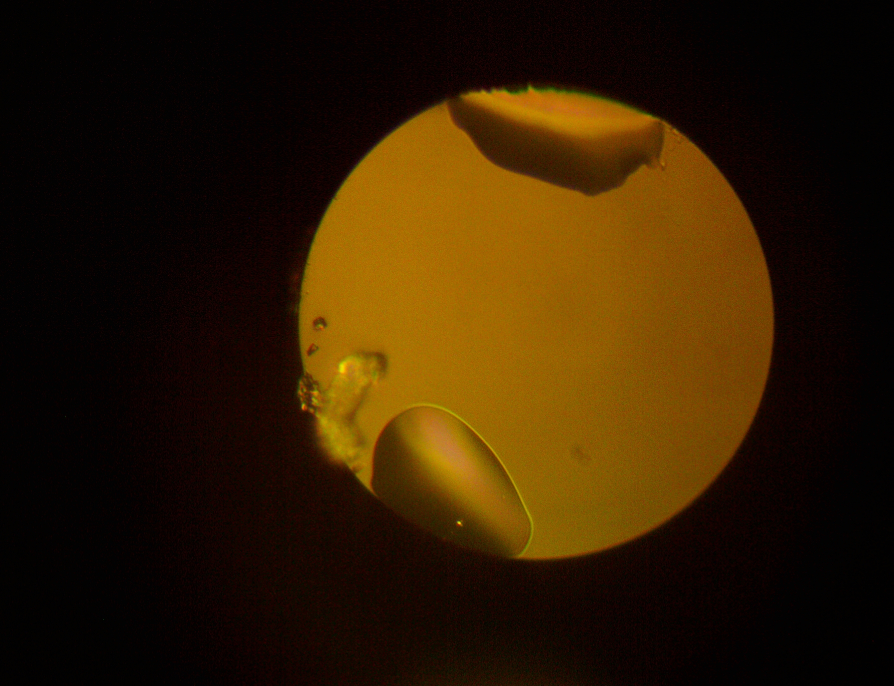
Photos/RemovableDesign4-1.jpg
