aorfi/URA2019/Photos/RemovableDesign5-2.jpg

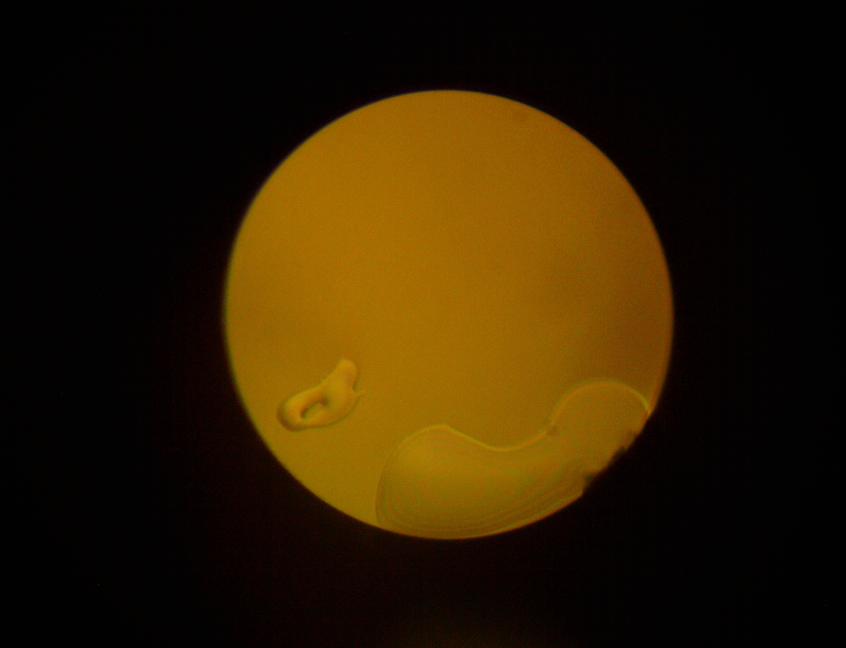
Photos/RemovableDesign5-2.jpg
