aorfi/URA2019/Photos/RemovableDesign6-1.jpg

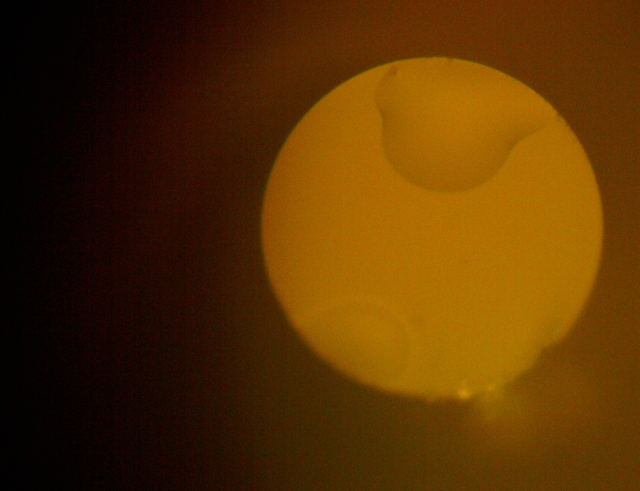
Photos/RemovableDesign6-1.jpg
