aorfi/URA2019/Photos/RemovableDesign6-2.jpg

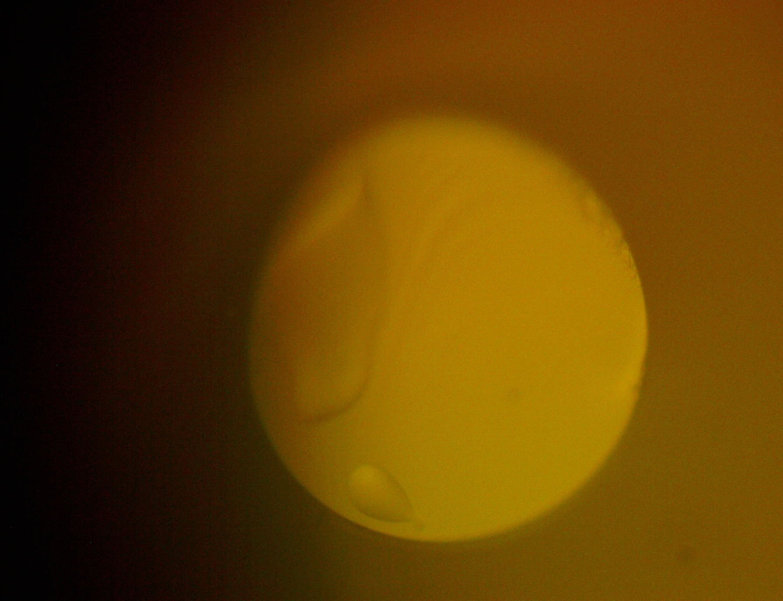
Photos/RemovableDesign6-2.jpg
