aorfi/URA2019/Photos/RemovableDesign7-1.jpg

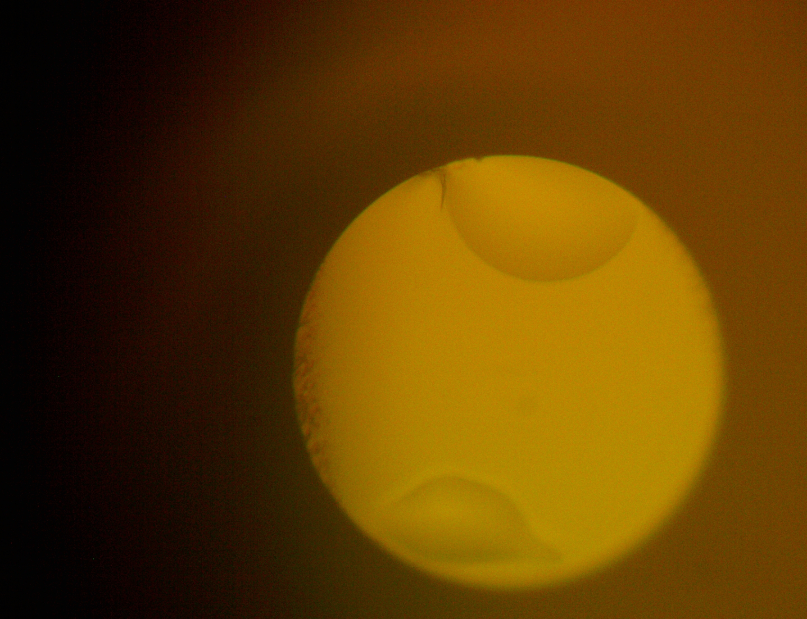
Photos/RemovableDesign7-1.jpg
