aorfi/URA2019/Photos/RemovableDesign8-2.jpg

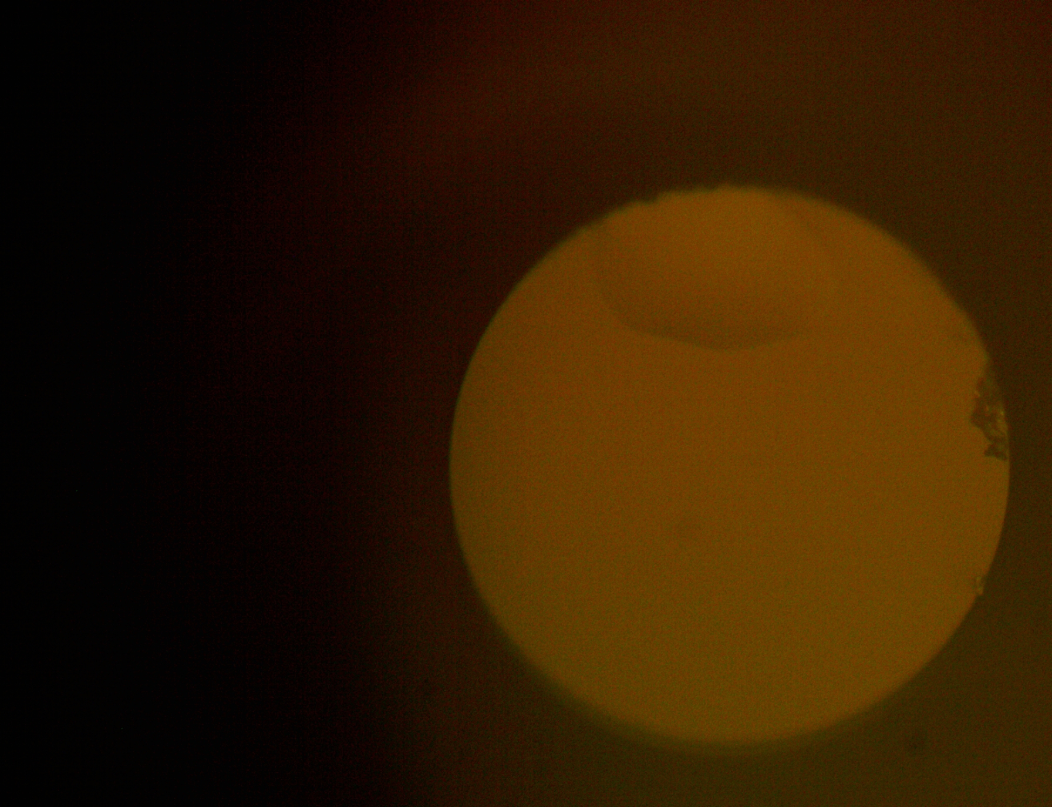
Photos/RemovableDesign8-2.jpg
