aorfi/URA2019/Photos/RemovableDesign9-2.jpg

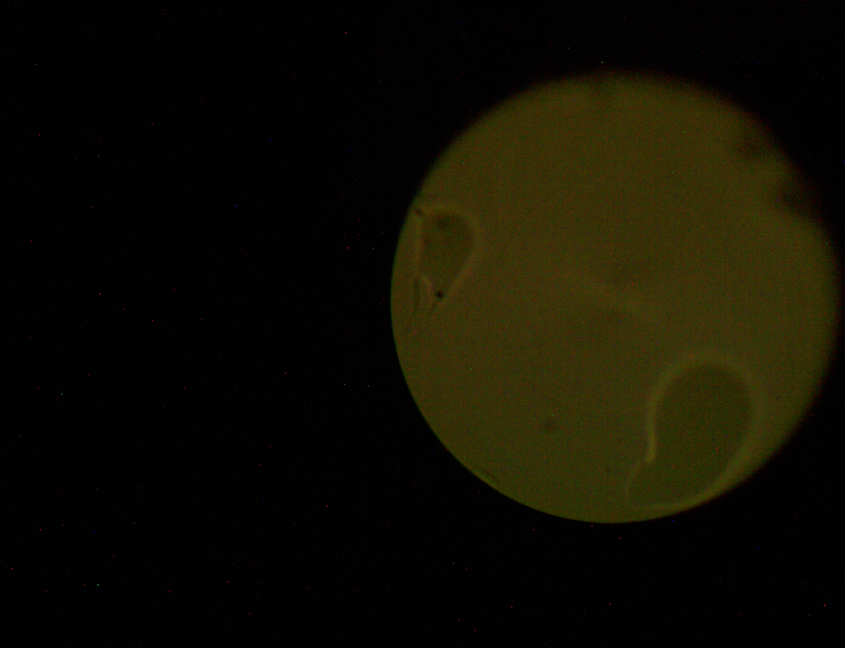
Photos/RemovableDesign9-2.jpg
