aorfi/URA2019/Photos/RemovableDesign10-2.jpg

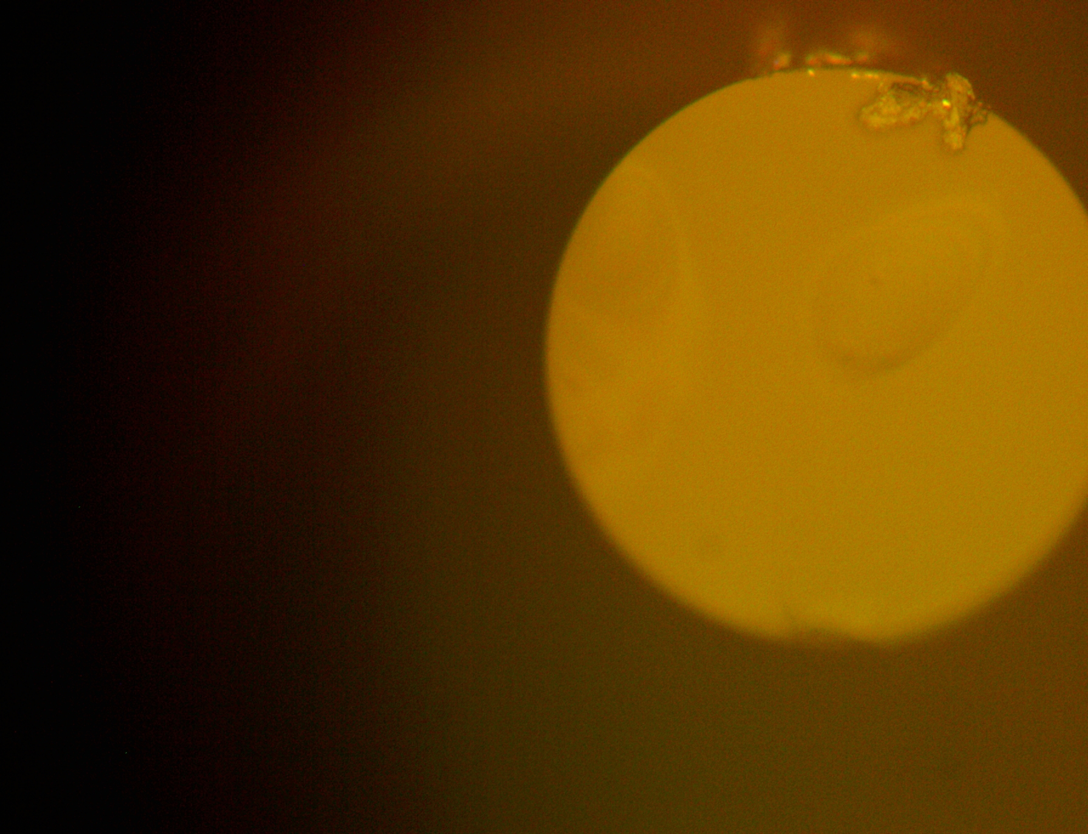
Photos/RemovableDesign10-2.jpg
