aorfi/URA2019/Photos/RemovableDesign11-1.jpg

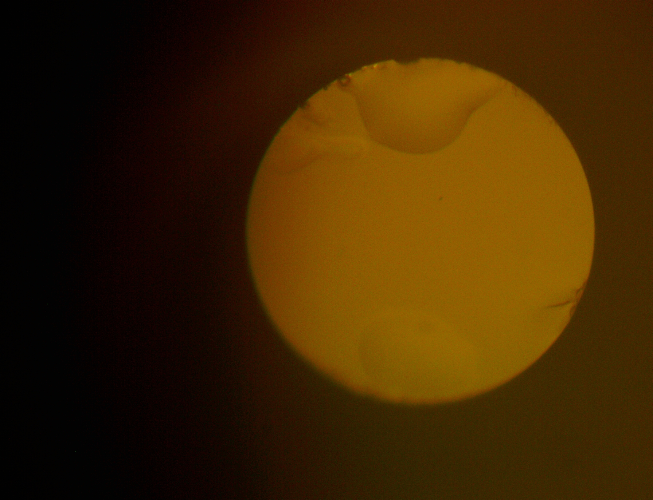
Photos/RemovableDesign11-1.jpg
