aorfi/URA2019/Photos/RemovableDesign12-1.jpg

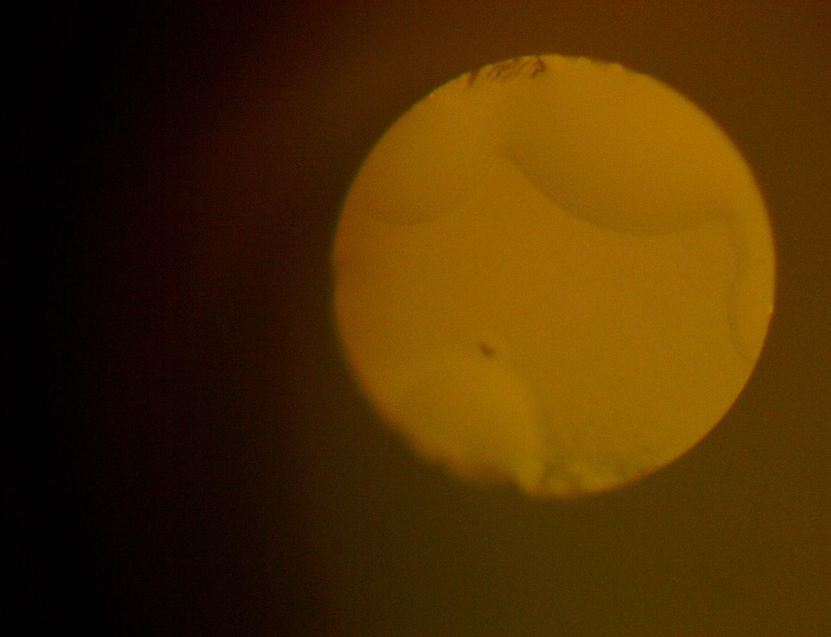
Photos/RemovableDesign12-1.jpg
