aorfi/URA2019/Photos/RemovableDesign12-2.jpg

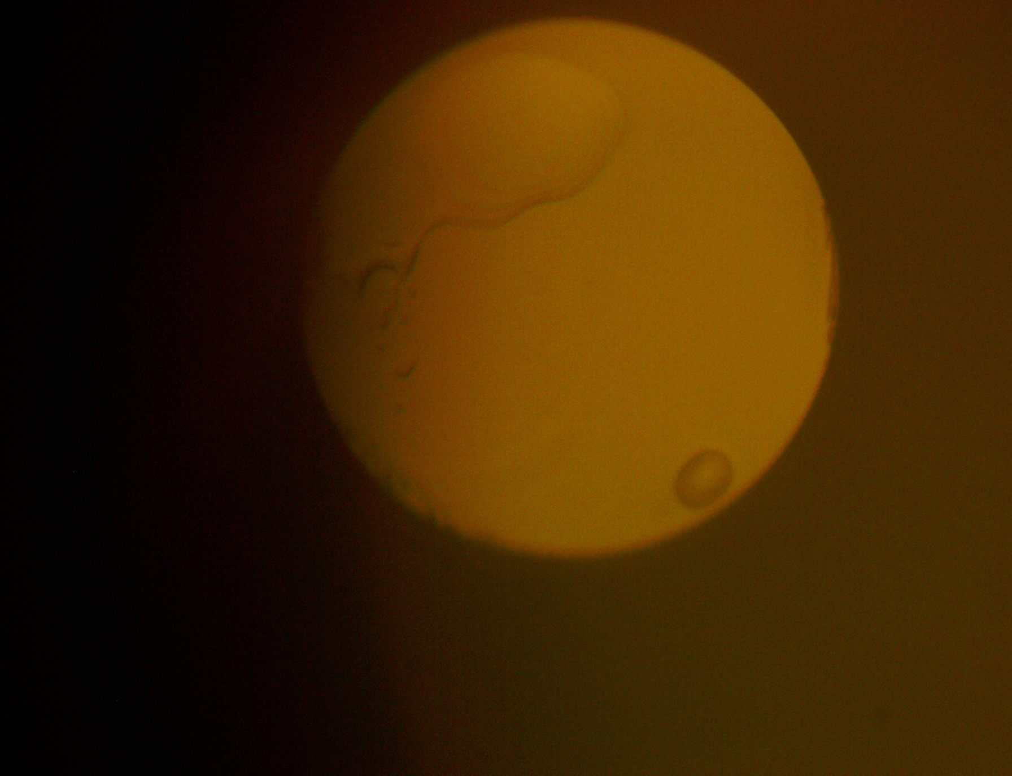
Photos/RemovableDesign12-2.jpg
