aorfi/URA2019/Photos/RemovableDesign13-2.jpg

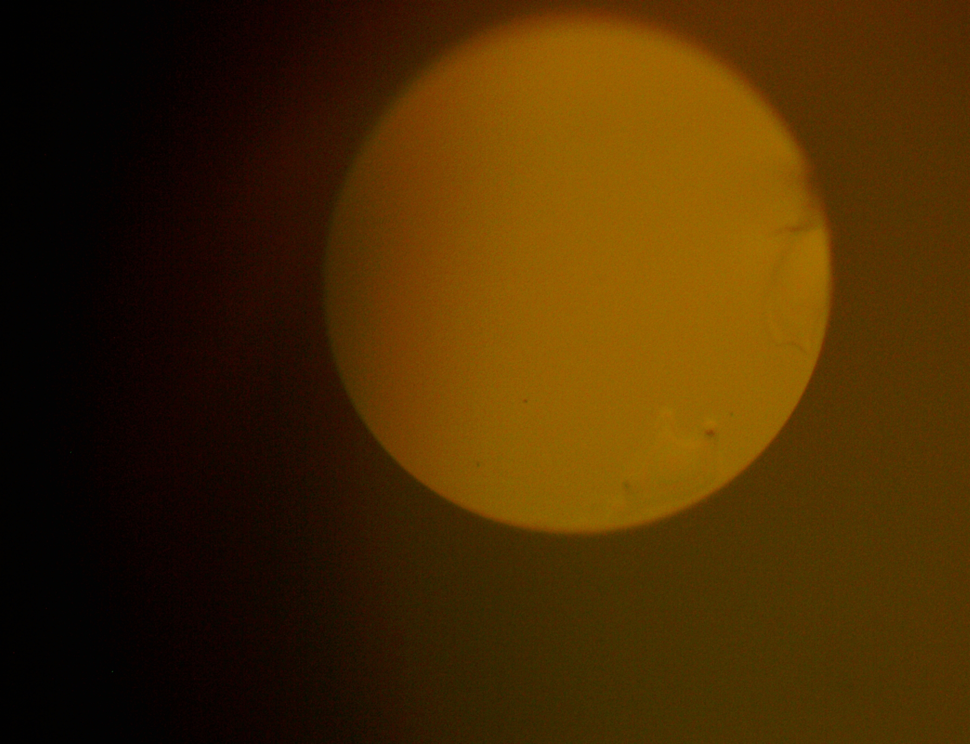
Photos/RemovableDesign13-2.jpg
