aorfi/URA2019/Photos/Scale2.jpg

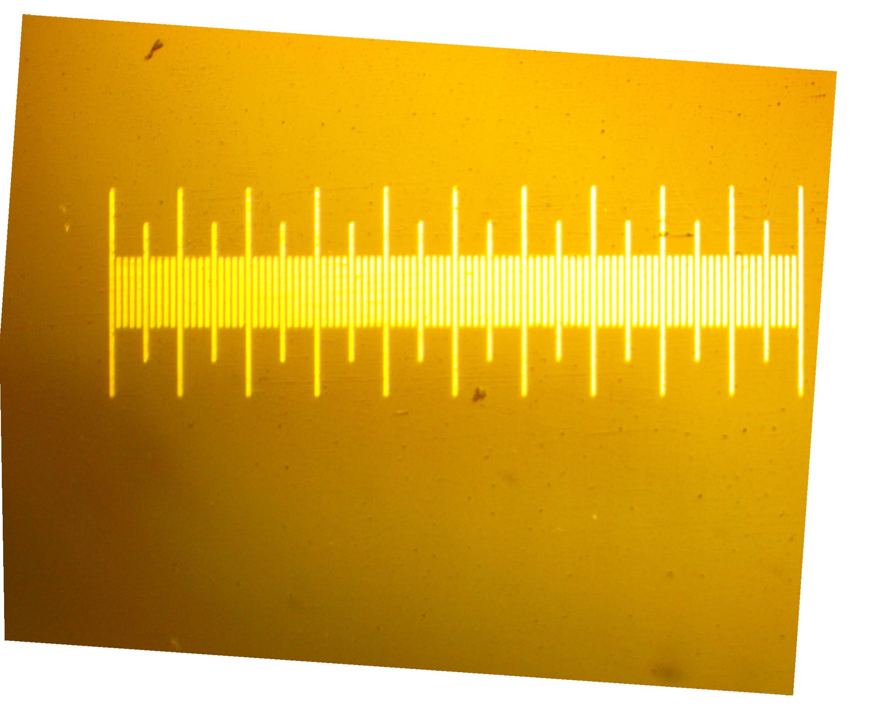
Photos/Scale2.jpg
