aorfi/URA2019/Photos/Scale10.jpg

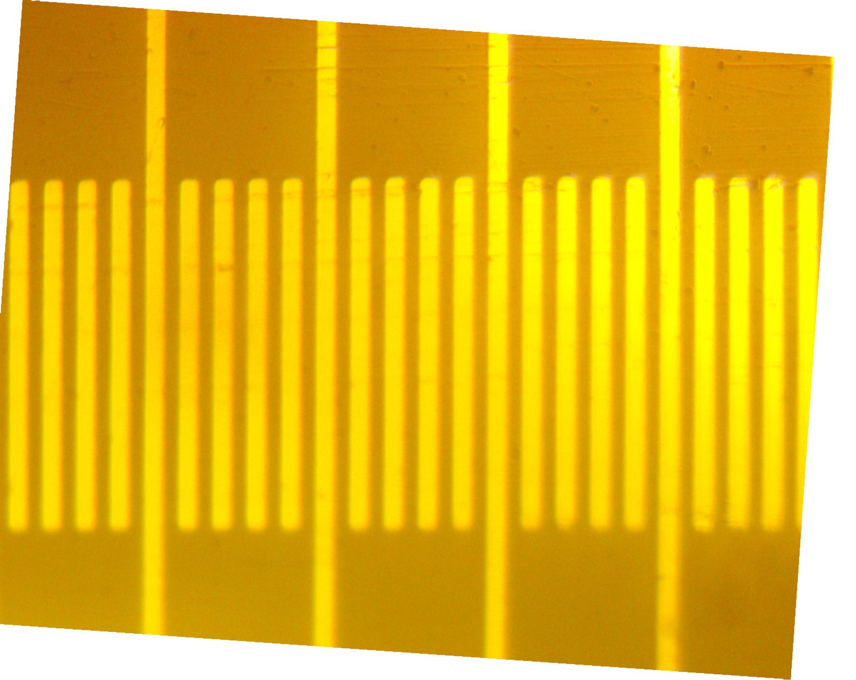
Photos/Scale10.jpg
