aorfi/URA2019/Photos/Scale.jpg

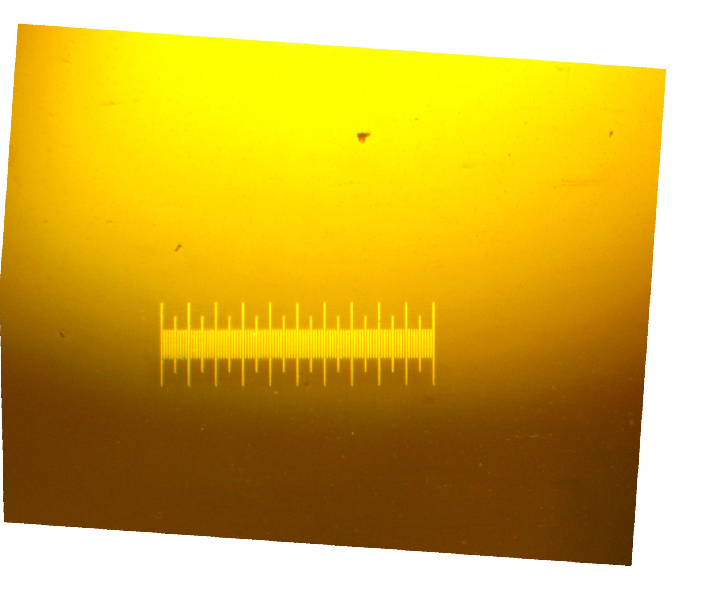
Photos/Scale.jpg
