aorfi/URA2019/Photos/ShortCure0.jpg

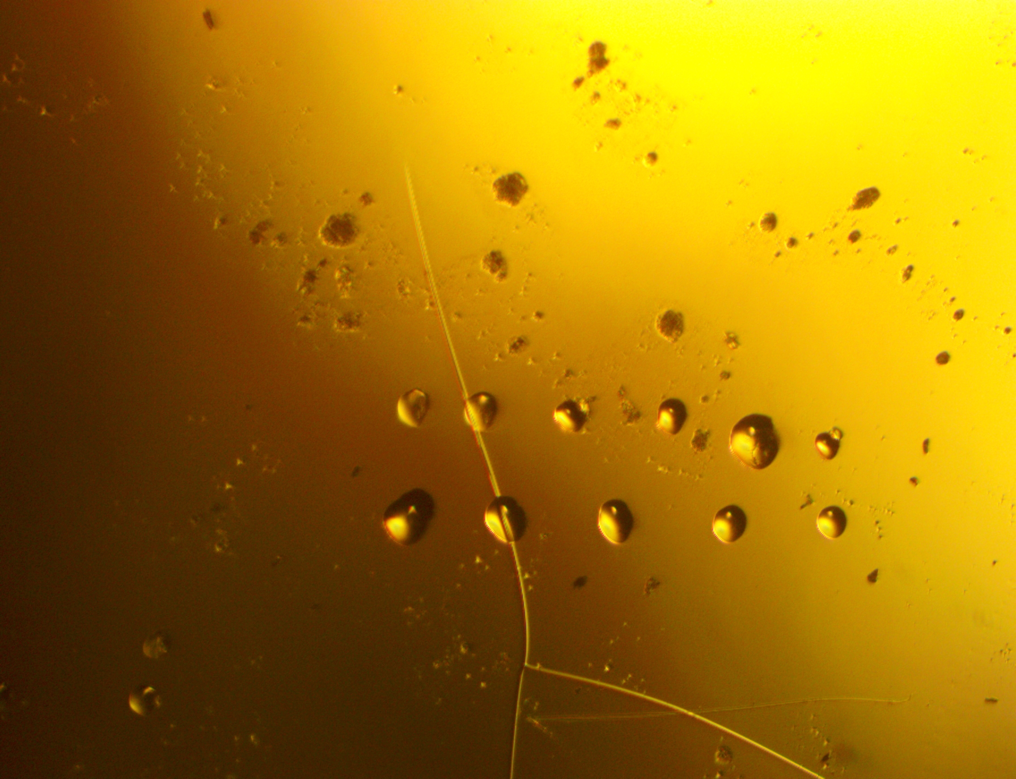
Photos/ShortCure0.jpg
