aorfi/URA2019/Photos/ShortCure30.jpg

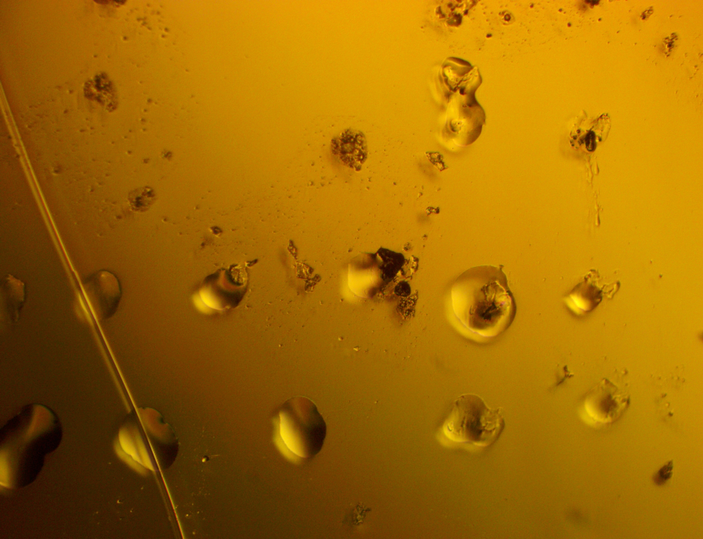
Photos/ShortCure30.jpg
