aorfi/URA2019/Photos/ShortCure45.jpg

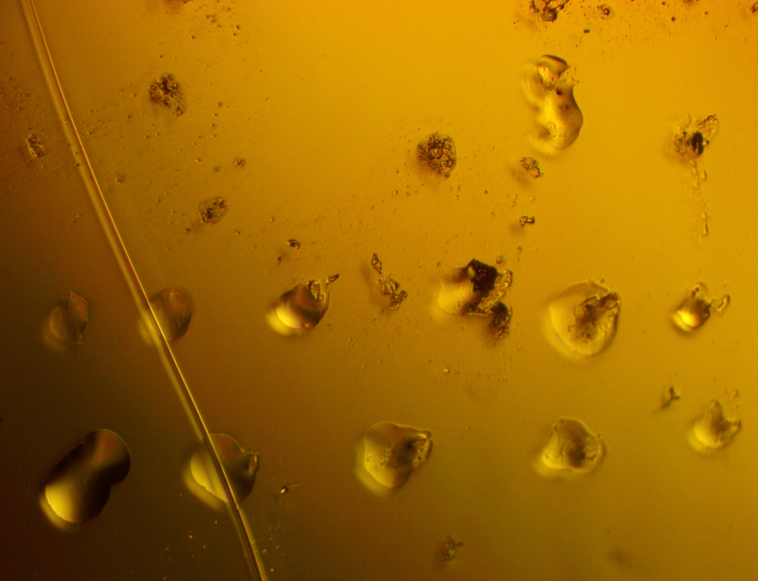
Photos/ShortCure45.jpg
