aorfi/URA2019/Photos/ShortCure60.jpg

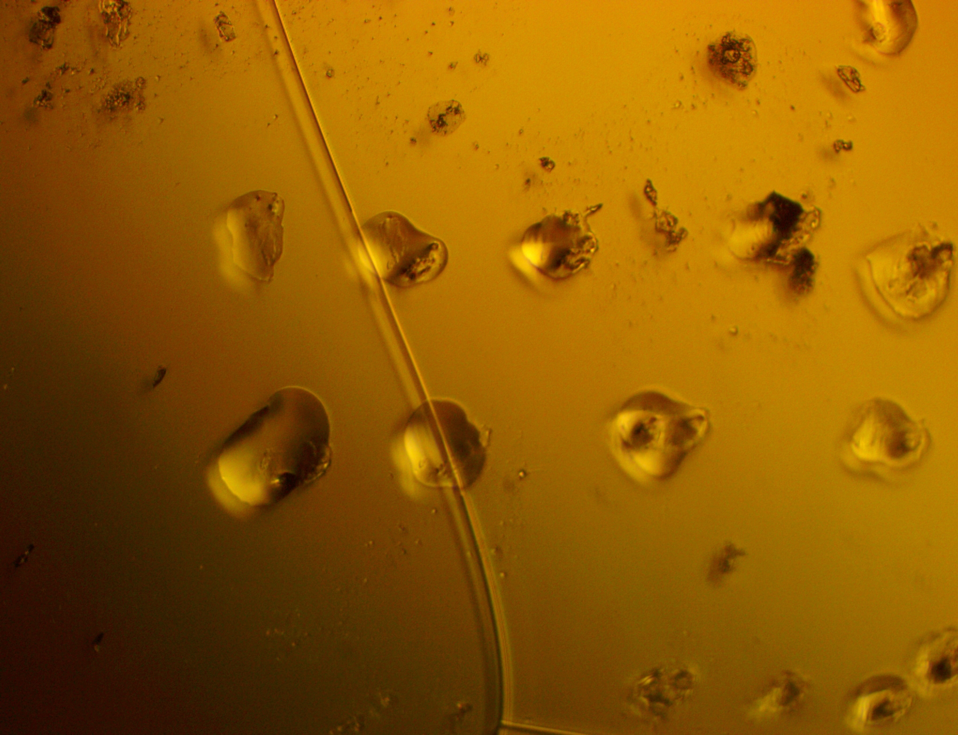
Photos/ShortCure60.jpg
