aorfi/URA2019/Photos/StraigtFibers.JPG

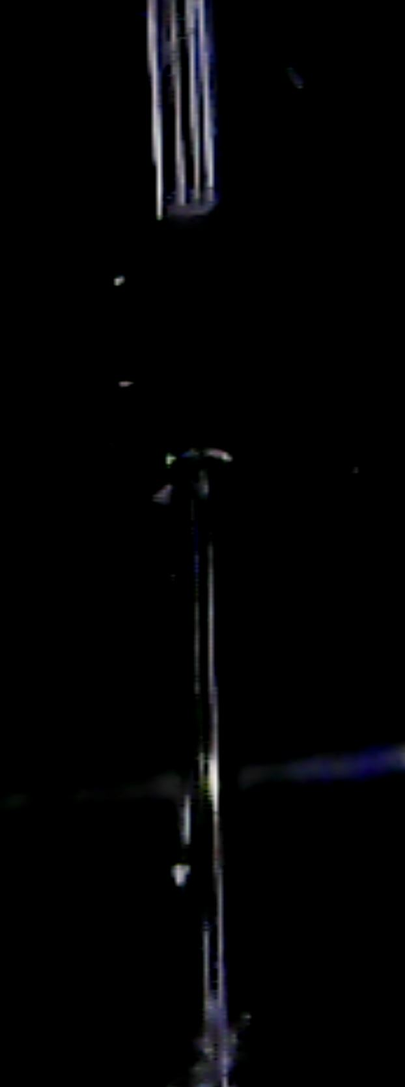
Photos/StraigtFibers.JPG
