aorfi/URA2019/Photos/Tip5.jpg

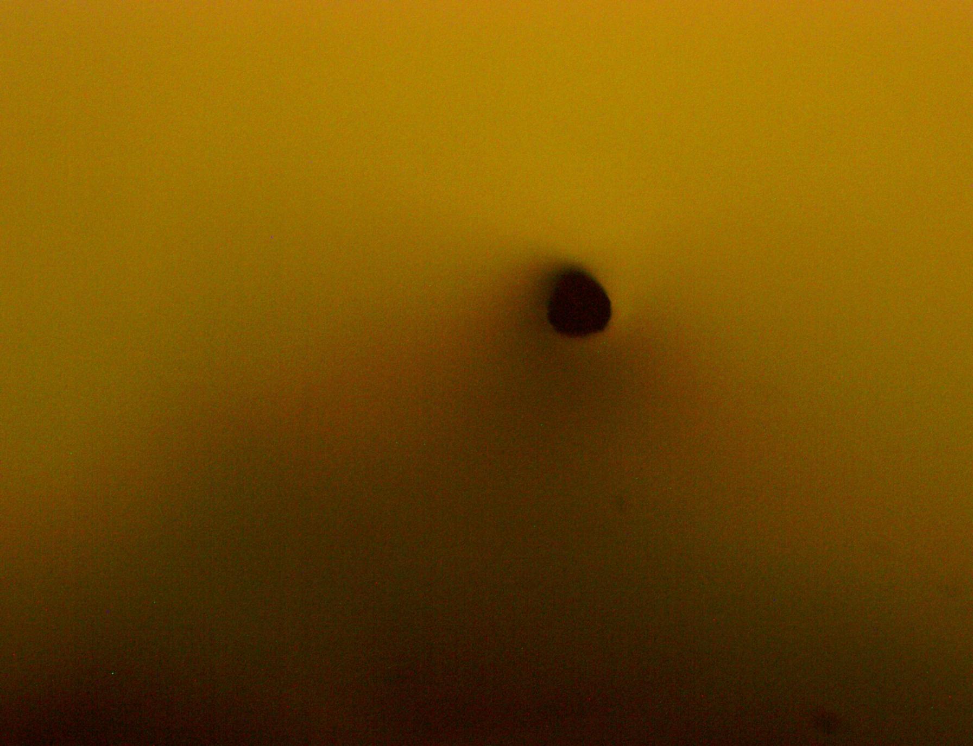
Photos/Tip5.jpg
