aorfi/URA2019/Photos/Tip.jpg

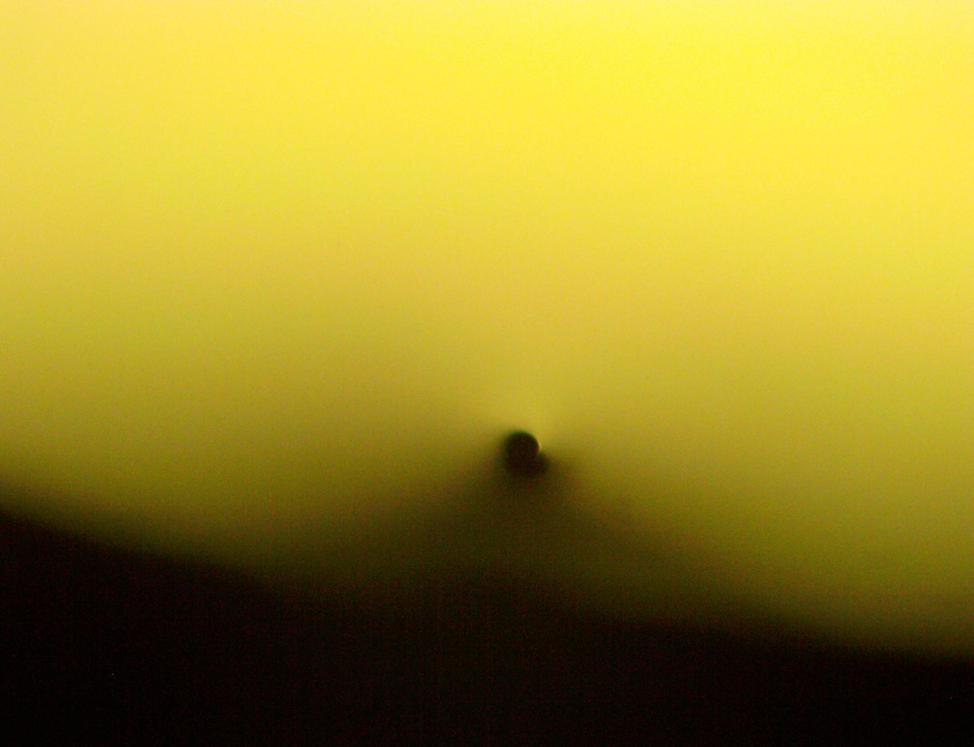
Photos/Tip.jpg
