aorfi/URA2019/Printing/Nut0.375-16.stl

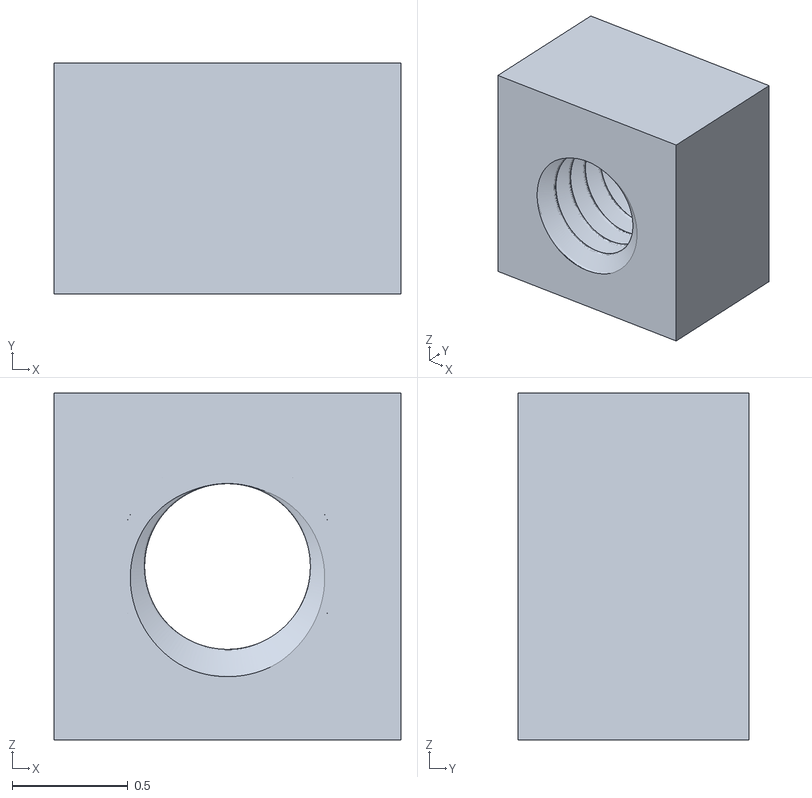
[picture p114: CAD file, 2019-08-08]
Printing/Nut0.375-16.stl
1.50 x 1.00 x 1.50
