aorfi/URA2019/Printing/Pawl2.stl

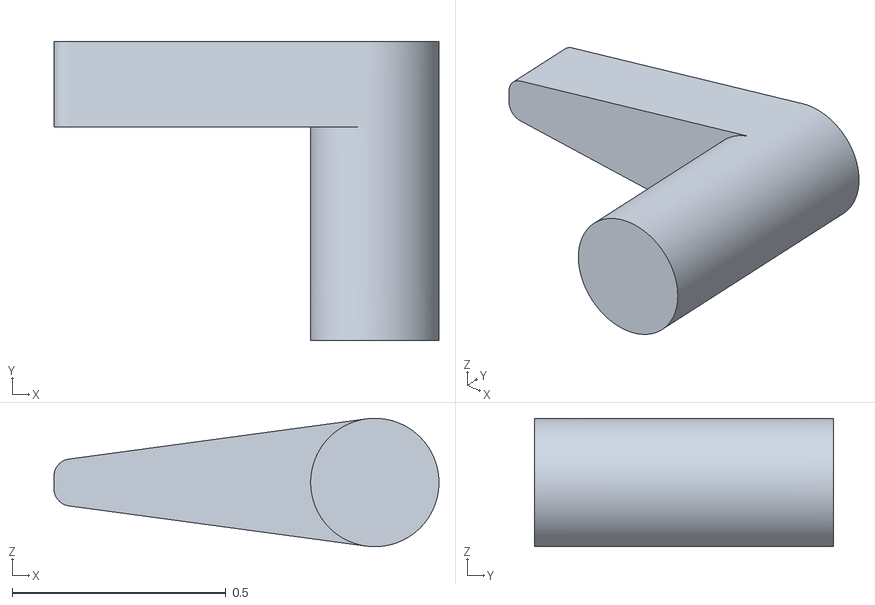
[picture p115: CAD file, 2019-08-08]
Printing/Pawl2.stl
0.9 x 0.7 x 0.3
