aorfi/URA2019/Printing/PinionHolderTest.stl

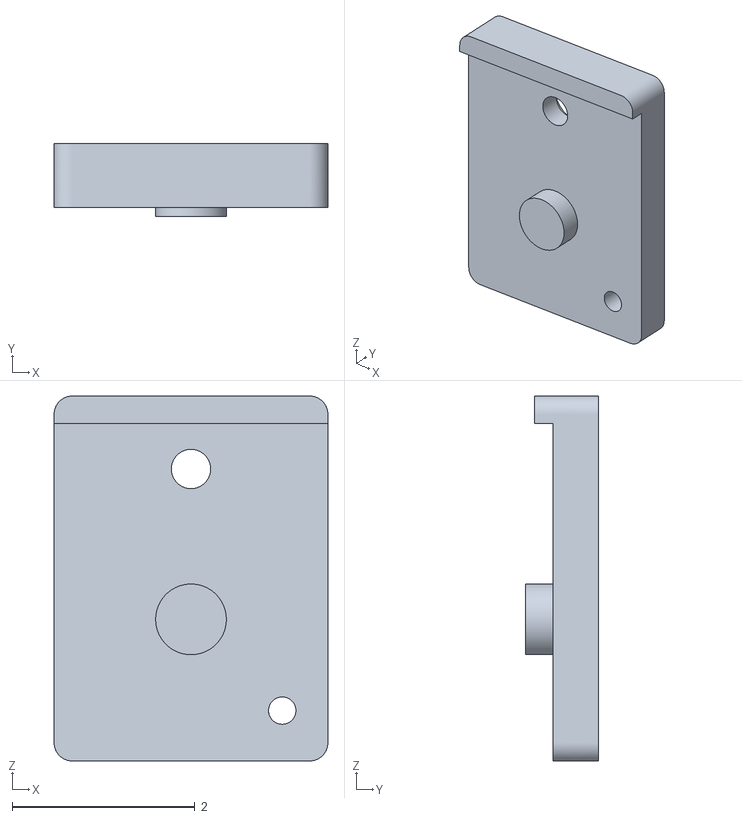
[picture p116: CAD file, 2019-08-08]
Printing/PinionHolderTest.stl
3.00 x 0.8 x 4.00
