aorfi/URA2019/Printing/ThreadTest0.375-16.stl

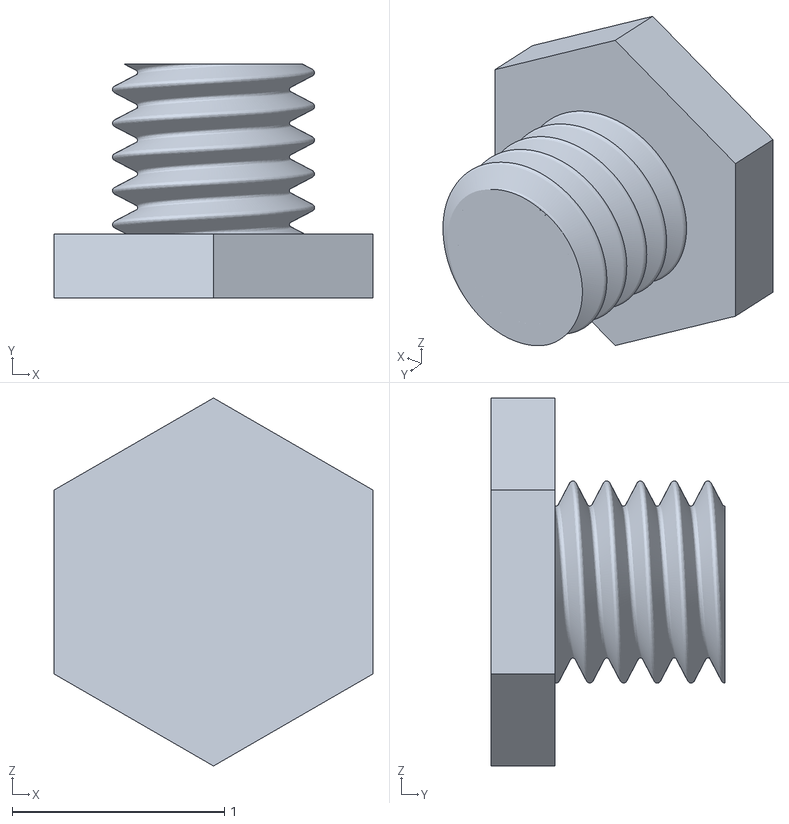
[picture p117: CAD file, 2019-08-08]
Printing/ThreadTest0.375-16.stl
1.50 x 1.10 x 1.73
