aorfi/URA2019/Printing/RackTest.stl

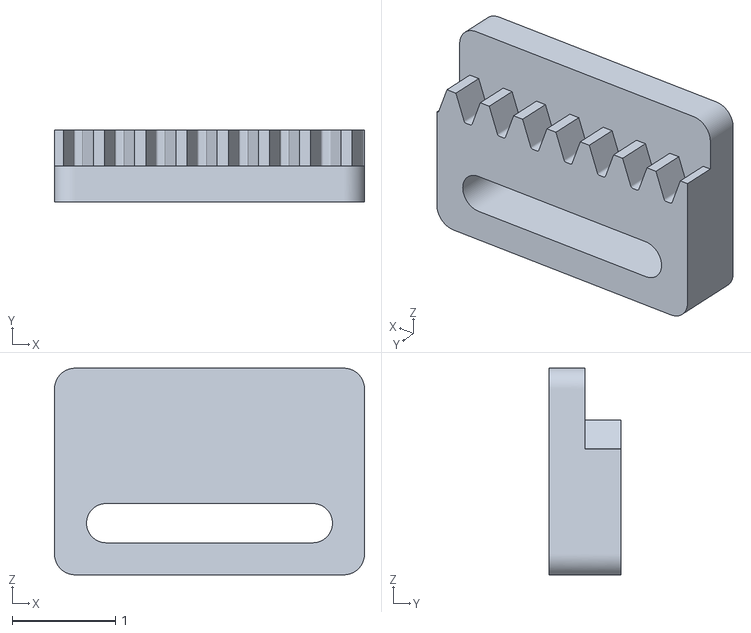
[picture p118: CAD file, 2019-08-08]
Printing/RackTest.stl
3.00 x 0.7 x 2.00
