aorfi/URA2019/Printing/ThreadTest0.25-20.stl

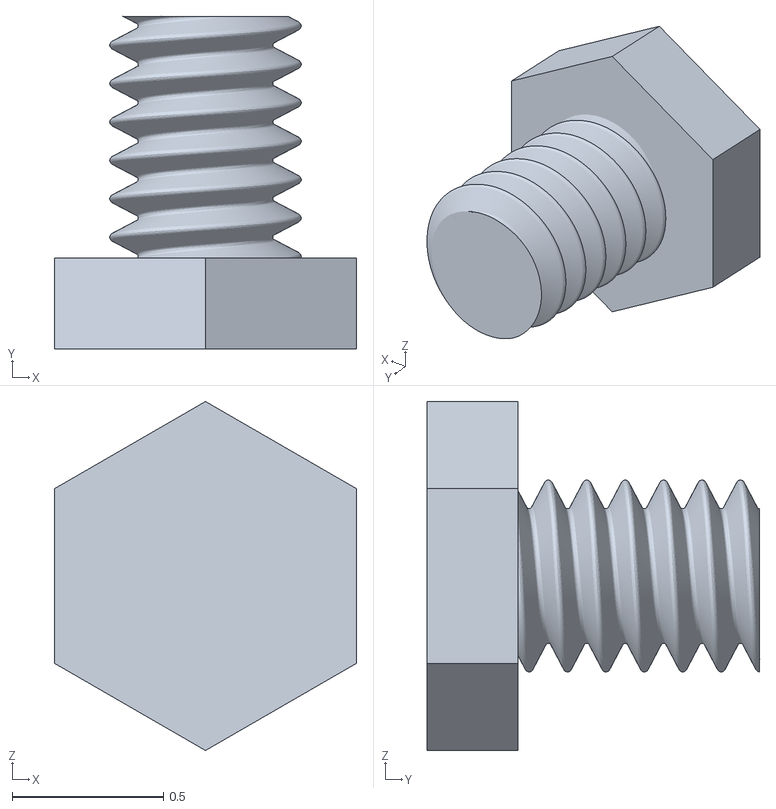
[picture p119: CAD file, 2019-08-06]
Printing/ThreadTest0.25-20.stl
1.00 x 1.10 x 1.15
