aorfi/URA2019/Printing/Pawl.stl

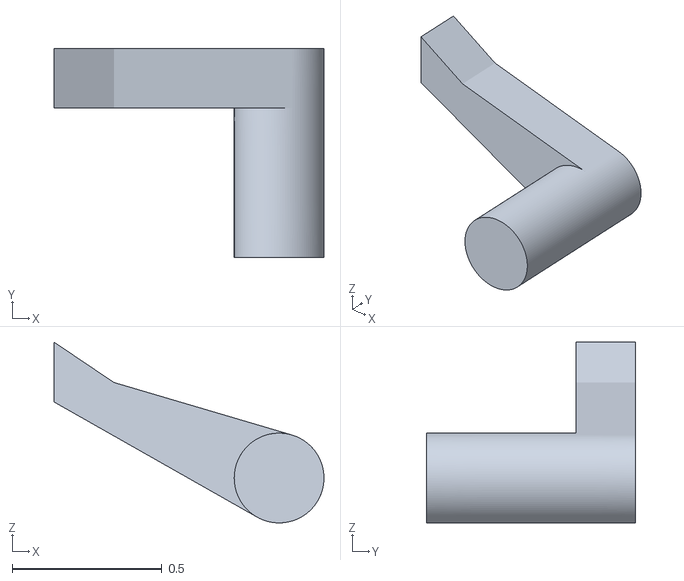
[picture p120: CAD file, 2019-08-06]
Printing/Pawl.stl
0.902 x 0.7 x 0.604
