aorfi/URA2019/Printing/Nut0.25-20.stl

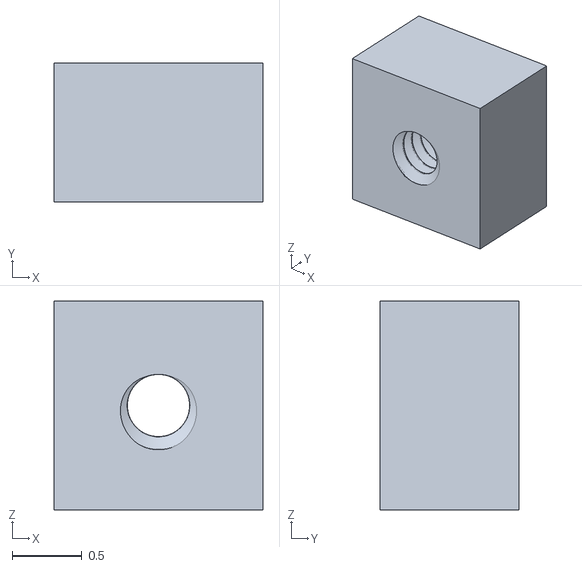
[picture p121: CAD file, 2019-08-06]
Printing/Nut0.25-20.stl
1.50 x 1.00 x 1.50
