aorfi/URA2019/Printing/BaseMount.stl

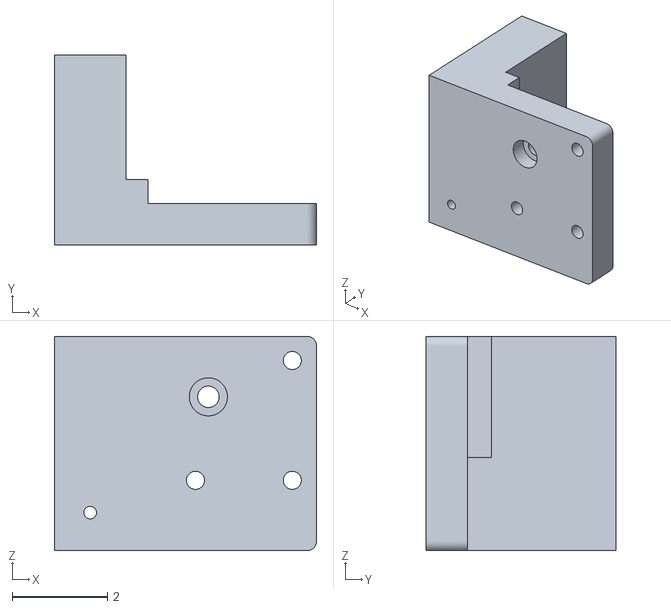
[picture p122: CAD file, 2019-08-02]
Printing/BaseMount.stl
5.50 x 3.99 x 4.50
