aorfi/URA2019/Printing/BearingMount.stl

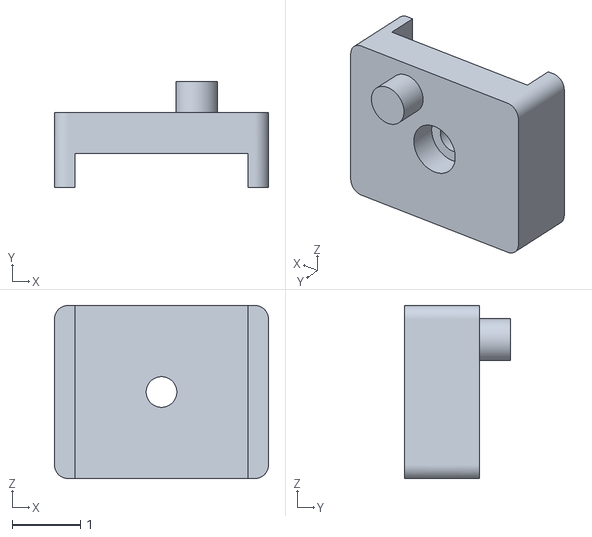
[picture p123: CAD file, 2019-07-31]
Printing/BearingMount.stl
3.14 x 1.56 x 2.54
