aorfi/URA2019/Printing/FixedFiber.stl

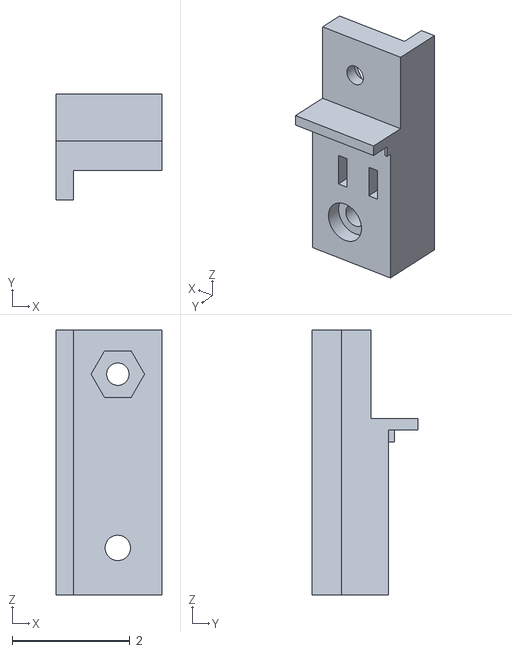
[picture p124: CAD file, 2019-07-31]
Printing/FixedFiber.stl
1.80 x 1.80 x 4.50
