aorfi/URA2019/Printing/CapillaryHolder.stl

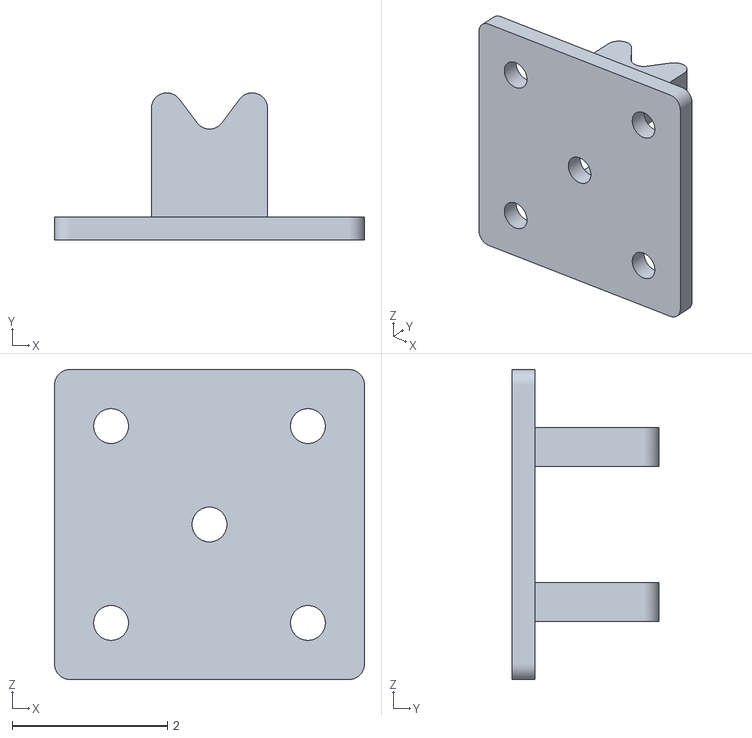
[picture p125: CAD file, 2019-07-31]
Printing/CapillaryHolder.stl
4.00 x 1.90 x 4.00
