aorfi/URA2019/Printing/PressFItTestHole.stl

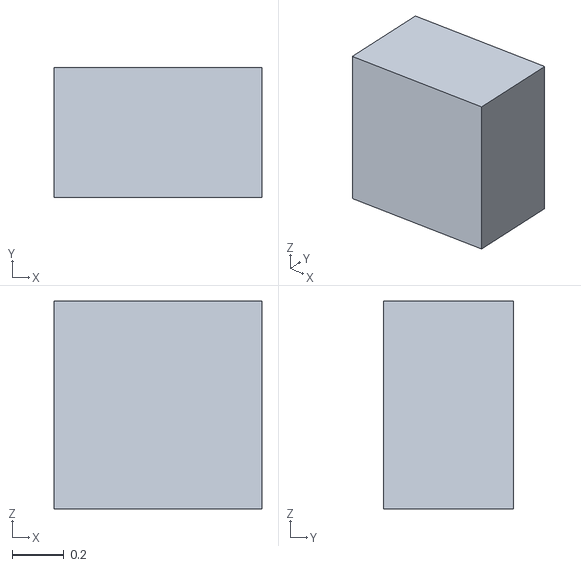
[picture p126: CAD file, 2019-07-23]
Printing/PressFItTestHole.stl
0.8 x 0.5 x 0.8
