aorfi/URA2019/Printing/PressFItTestPeg.stl

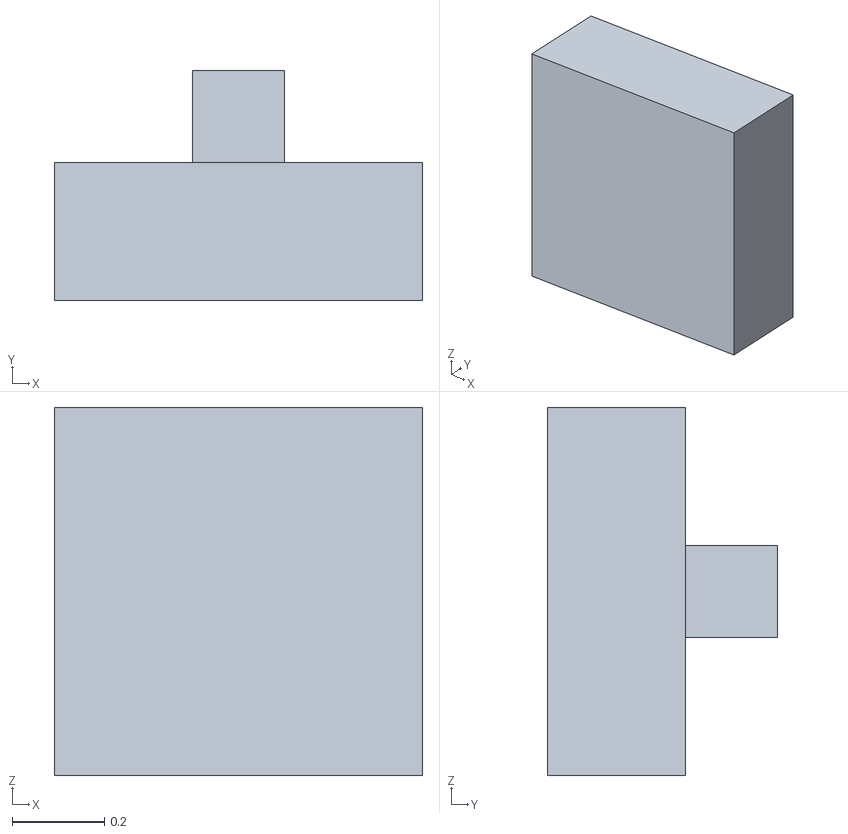
[picture p127: CAD file, 2019-07-23]
Printing/PressFItTestPeg.stl
0.8 x 0.5 x 0.8
