aorfi/URA2019/Printing/FixedFiber2.stl

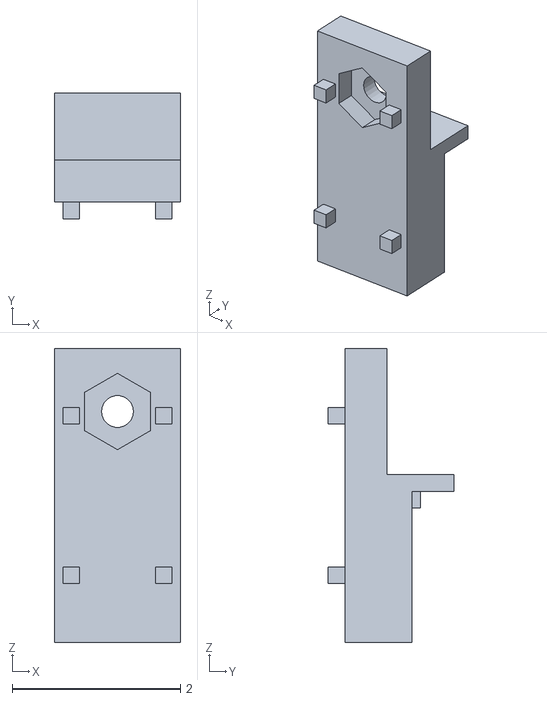
[picture p128: CAD file, 2019-07-23]
Printing/FixedFiber2.stl
1.50 x 1.50 x 3.50
