aorfi/URA2019/Printing/CameraClamp.stl

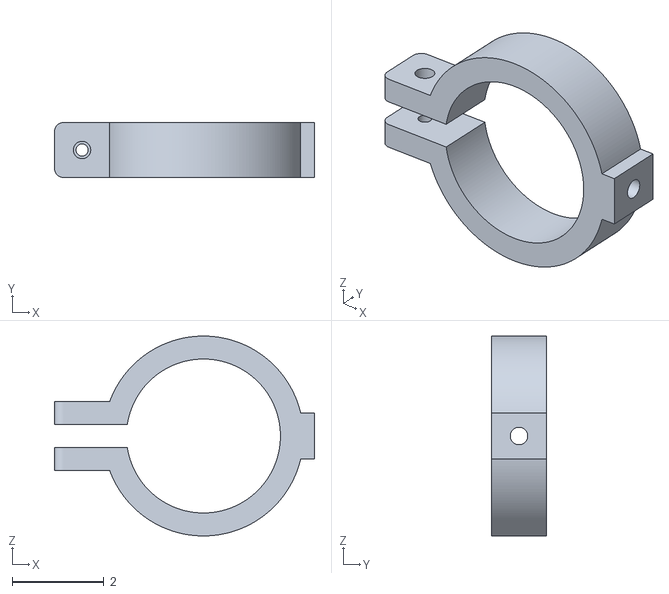
[picture p129: CAD file, 2019-07-23]
Printing/CameraClamp.stl
5.66 x 1.20 x 4.35
