aorfi/URA2019/Printing/CameraSlider.stl

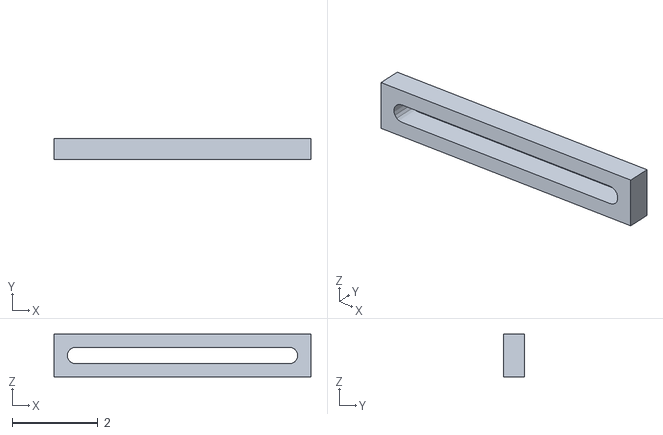
[picture p130: CAD file, 2019-07-23]
Printing/CameraSlider.stl
6.00 x 0.5 x 1.00
