aorfi/URA2019/Printing/FiberMount2.stl

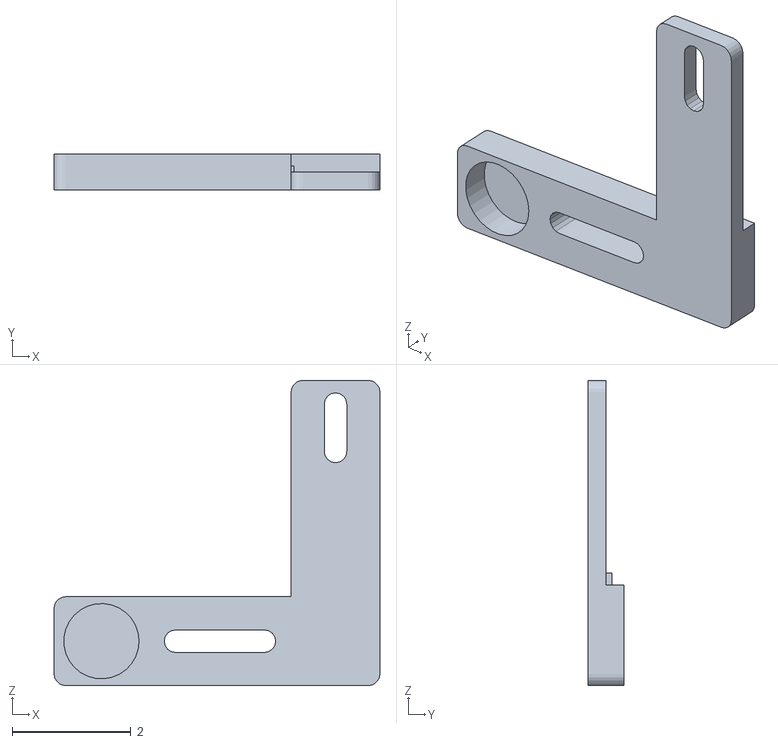
[picture p131: CAD file, 2019-07-23]
Printing/FiberMount2.stl
5.50 x 0.6 x 5.15
