aorfi/URA2019/Printing/PressFItTestHex.stl

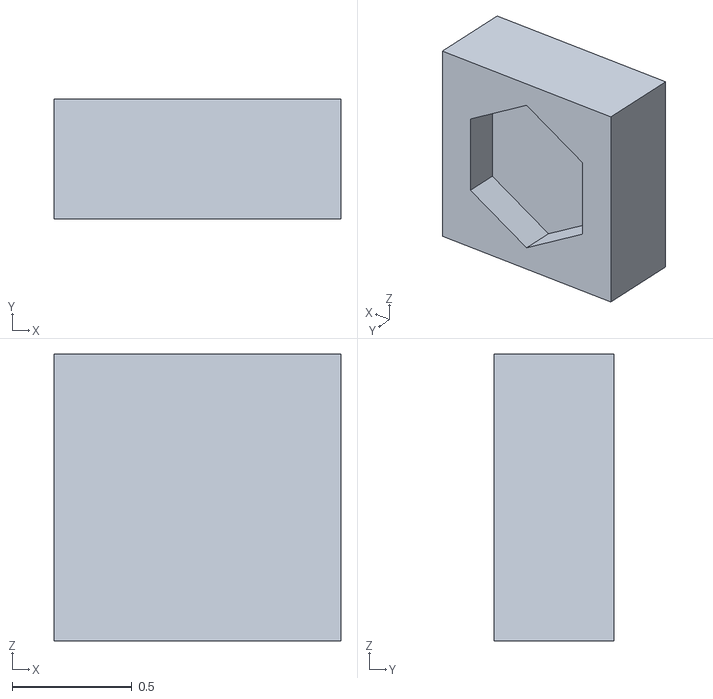
[picture p132: CAD file, 2019-07-23]
Printing/PressFItTestHex.stl
1.20 x 0.5 x 1.20
