aorfi/URA2019/Printing/FiberMount.stl

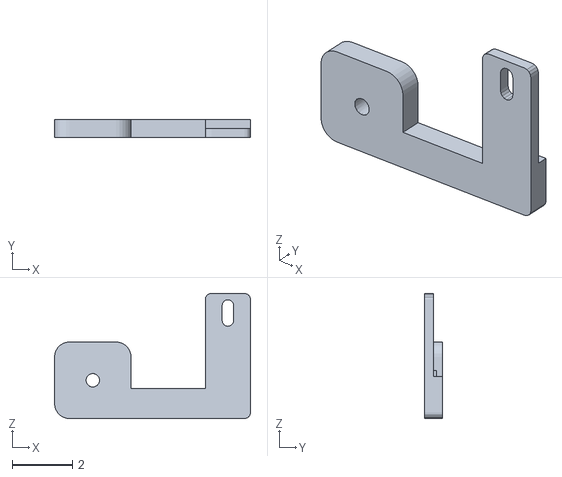
[picture p133: CAD file, 2019-07-02]
Printing/FiberMount.stl
6.50 x 0.6 x 4.15
