aorfi/URA2019/Printing/RemovableAlignmentPiece.stl

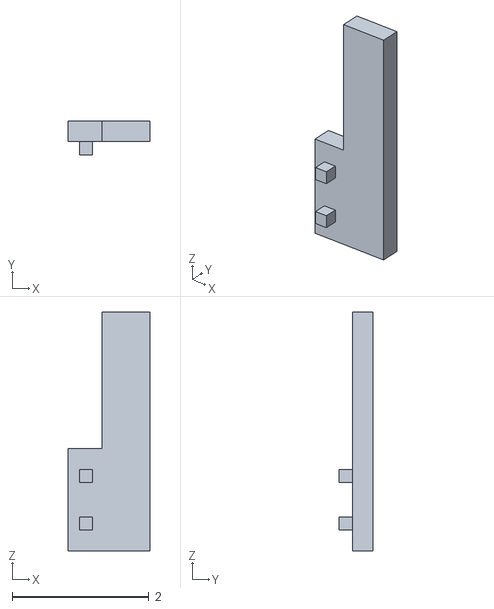
[picture p134: CAD file, 2019-06-21]
Printing/RemovableAlignmentPiece.stl
1.20 x 0.5 x 3.50
