aorfi/URA2019/Printing/AlignmentPiece.stl

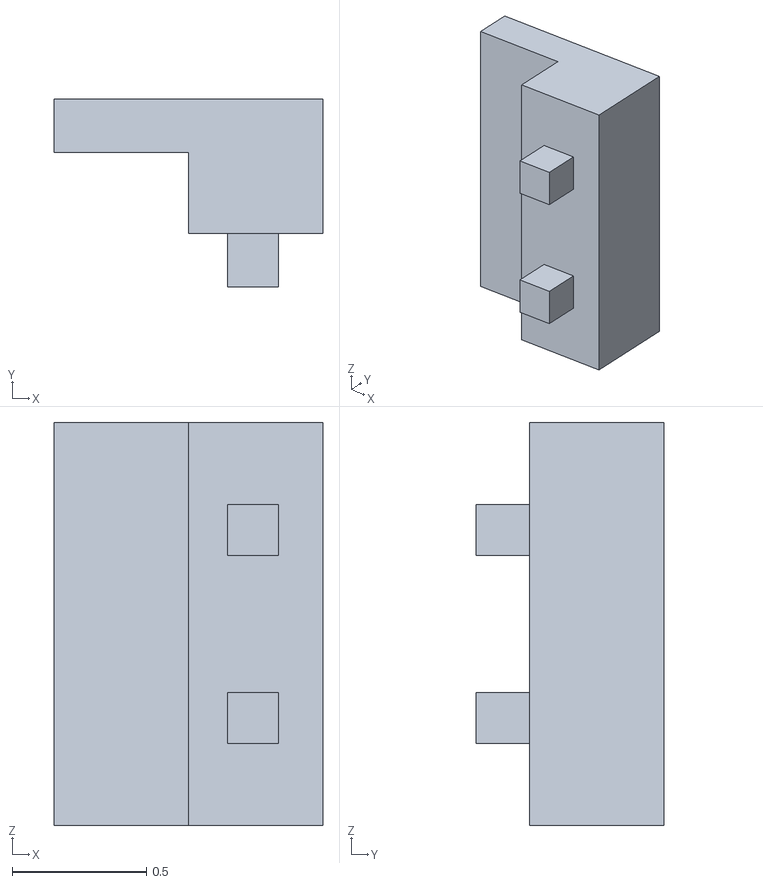
[picture p135: CAD file, 2019-06-21]
Printing/AlignmentPiece.stl
1.00 x 0.7 x 1.50
