aorfi/URA2019/Printing/ChipPusher.stl

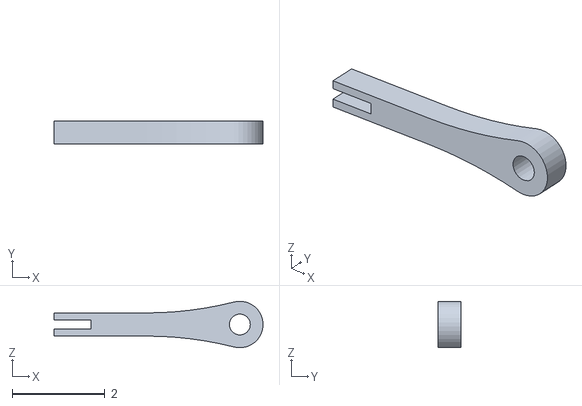
[picture p136: CAD file, 2019-06-18]
Printing/ChipPusher.stl
4.50 x 0.5 x 0.998
