aorfi/URA2019/Photos/cameraSetup1.PNG

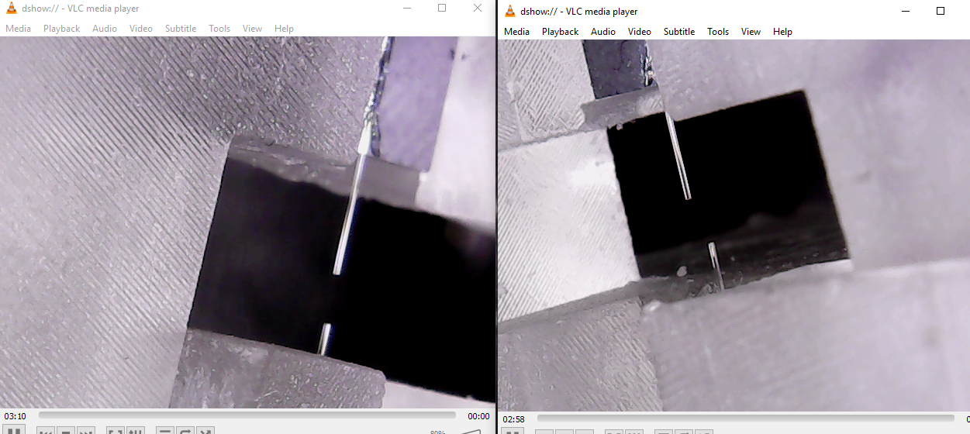
Photos/cameraSetup1.PNG
