aorfi/URA2019/Photos/cameraSetup2.PNG

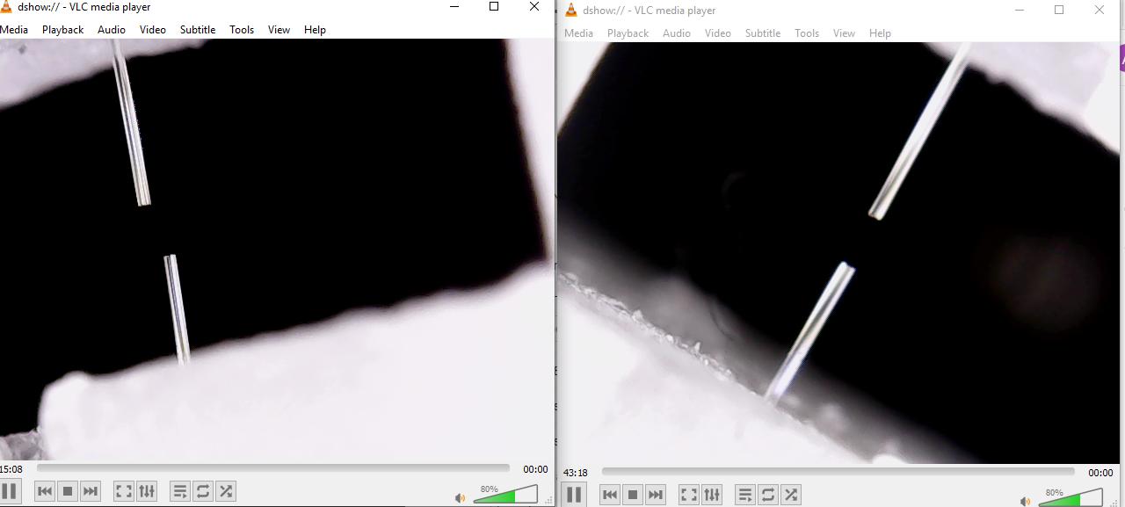
Photos/cameraSetup2.PNG
